fabianhartmann2/LandyHeater-Board/hardware/01_Power_Input_USB.kicad_sch

## KiCad design hardware/01_Power_Input_USB.kicad_sch (2026-09-07, an earlier design)

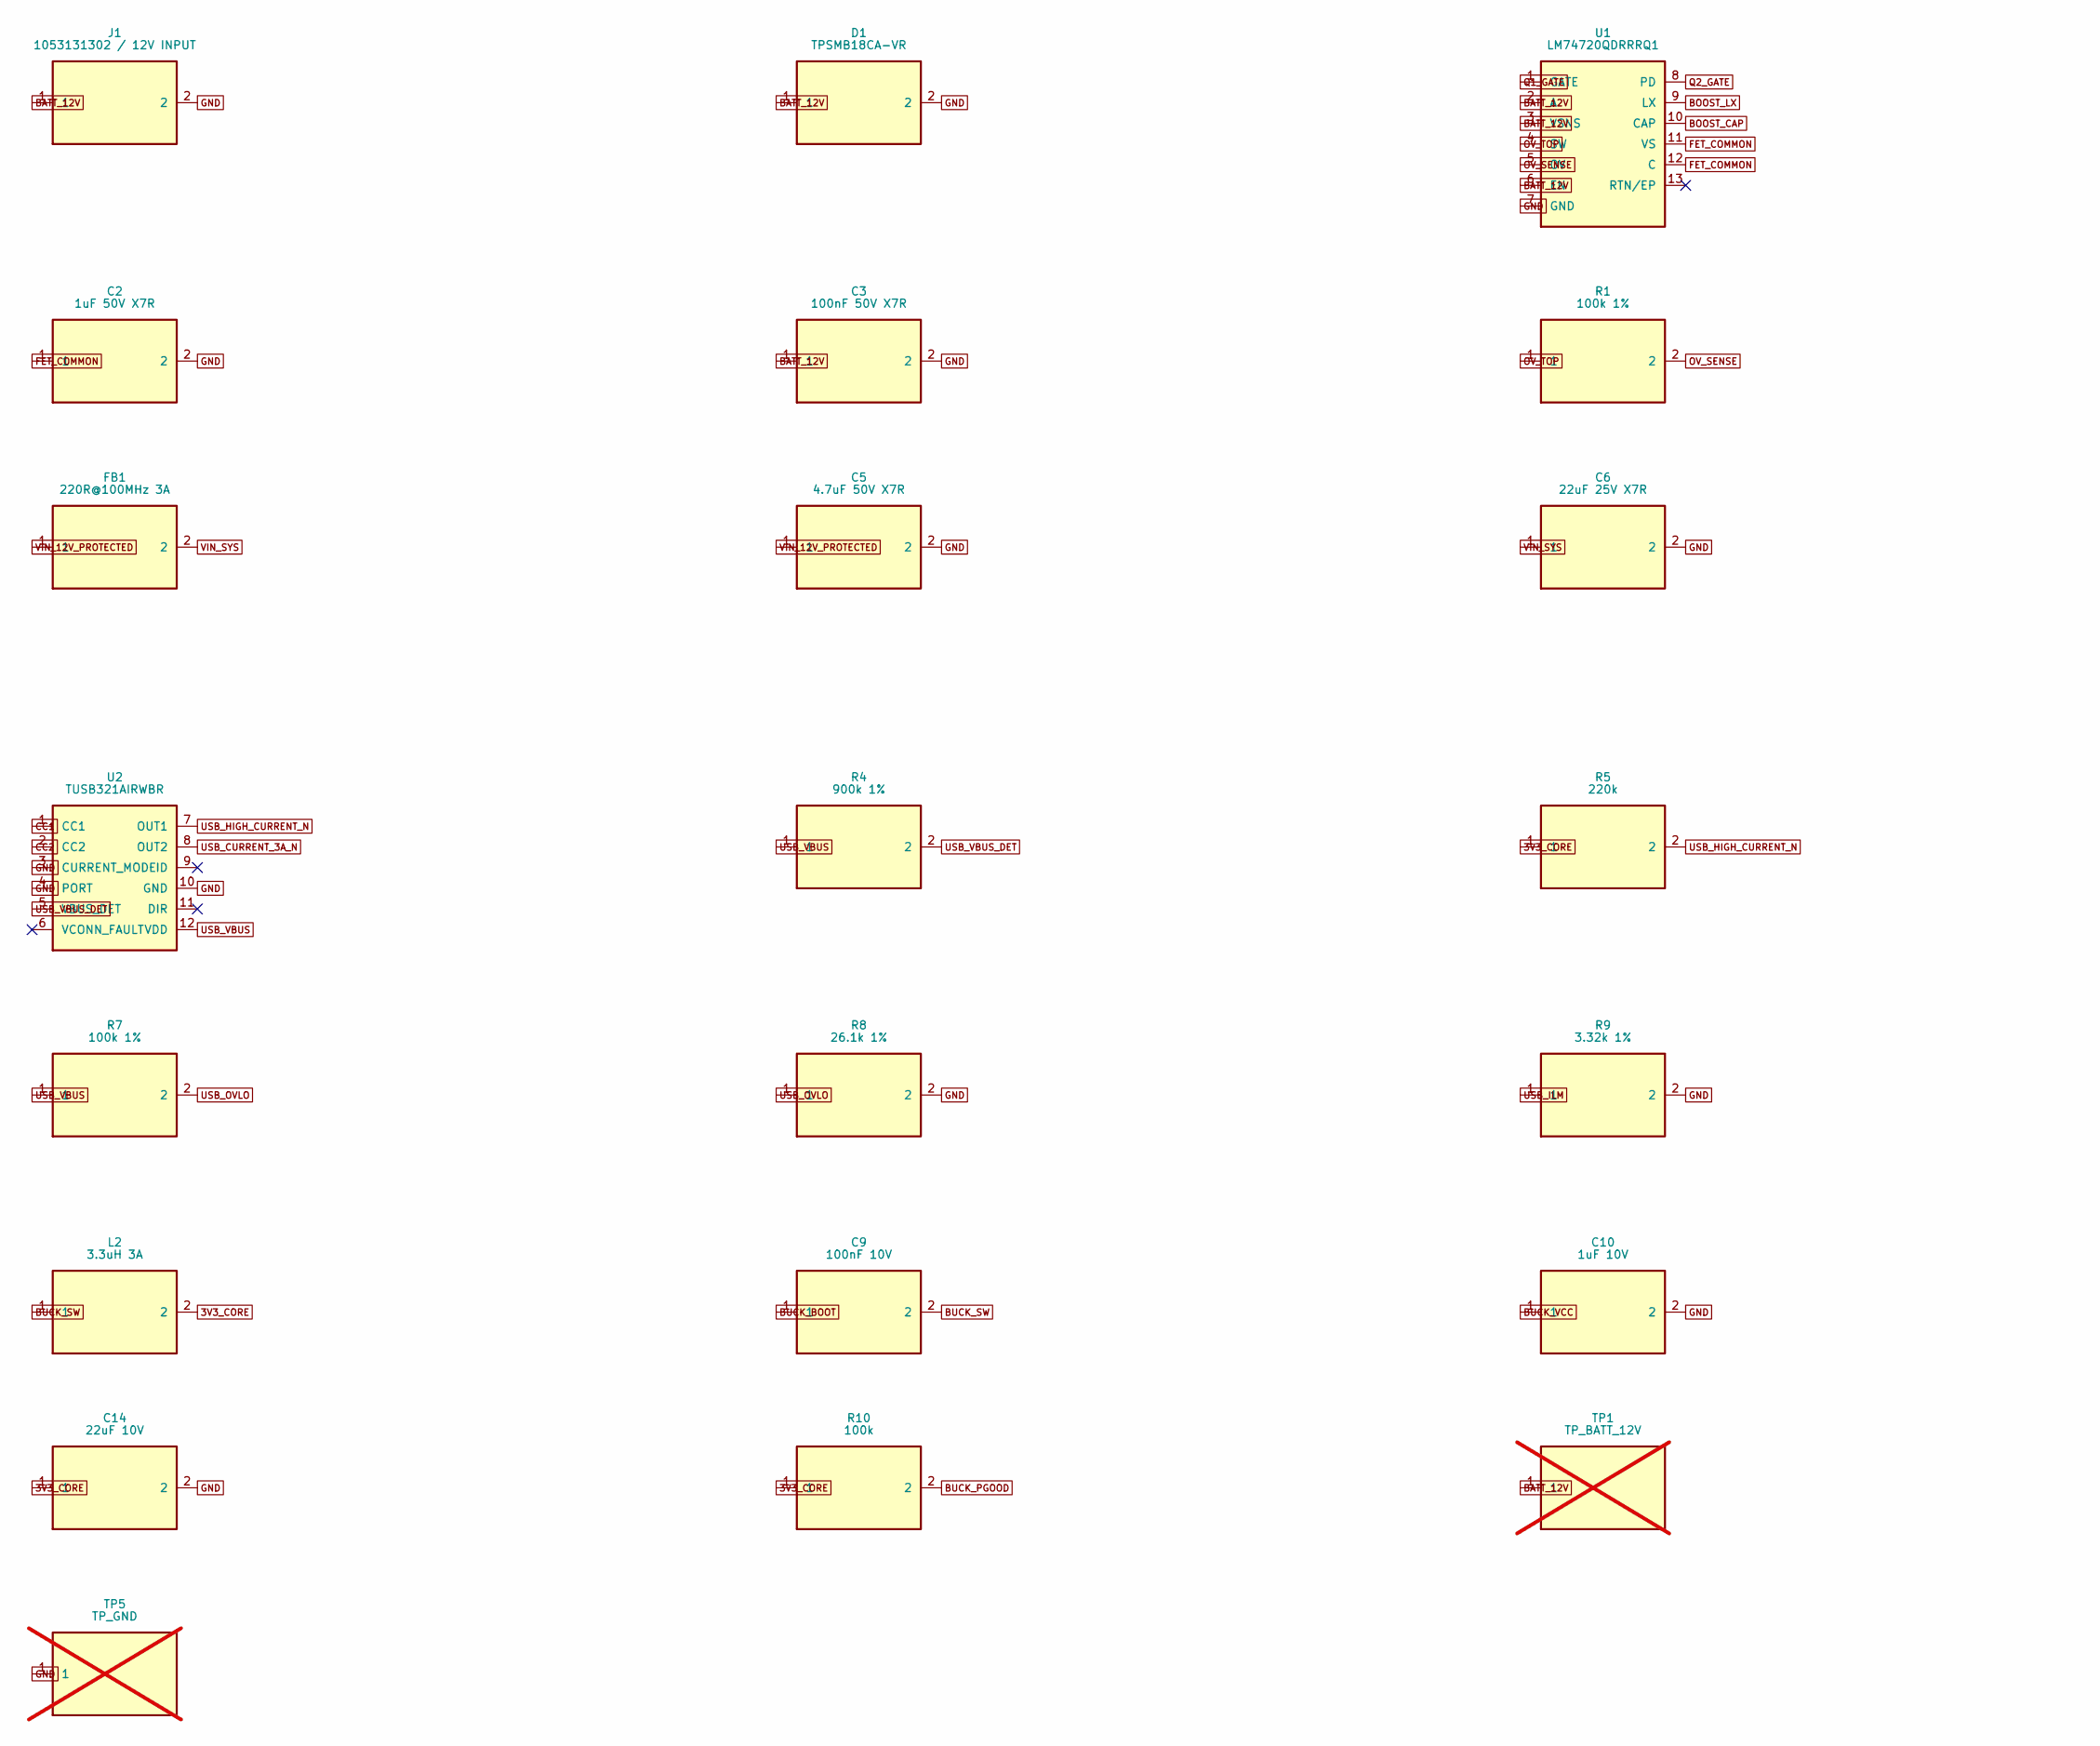
[picture p8: schematic 01_Power_Input_USB.kicad_sch, part in row 1, column 1]

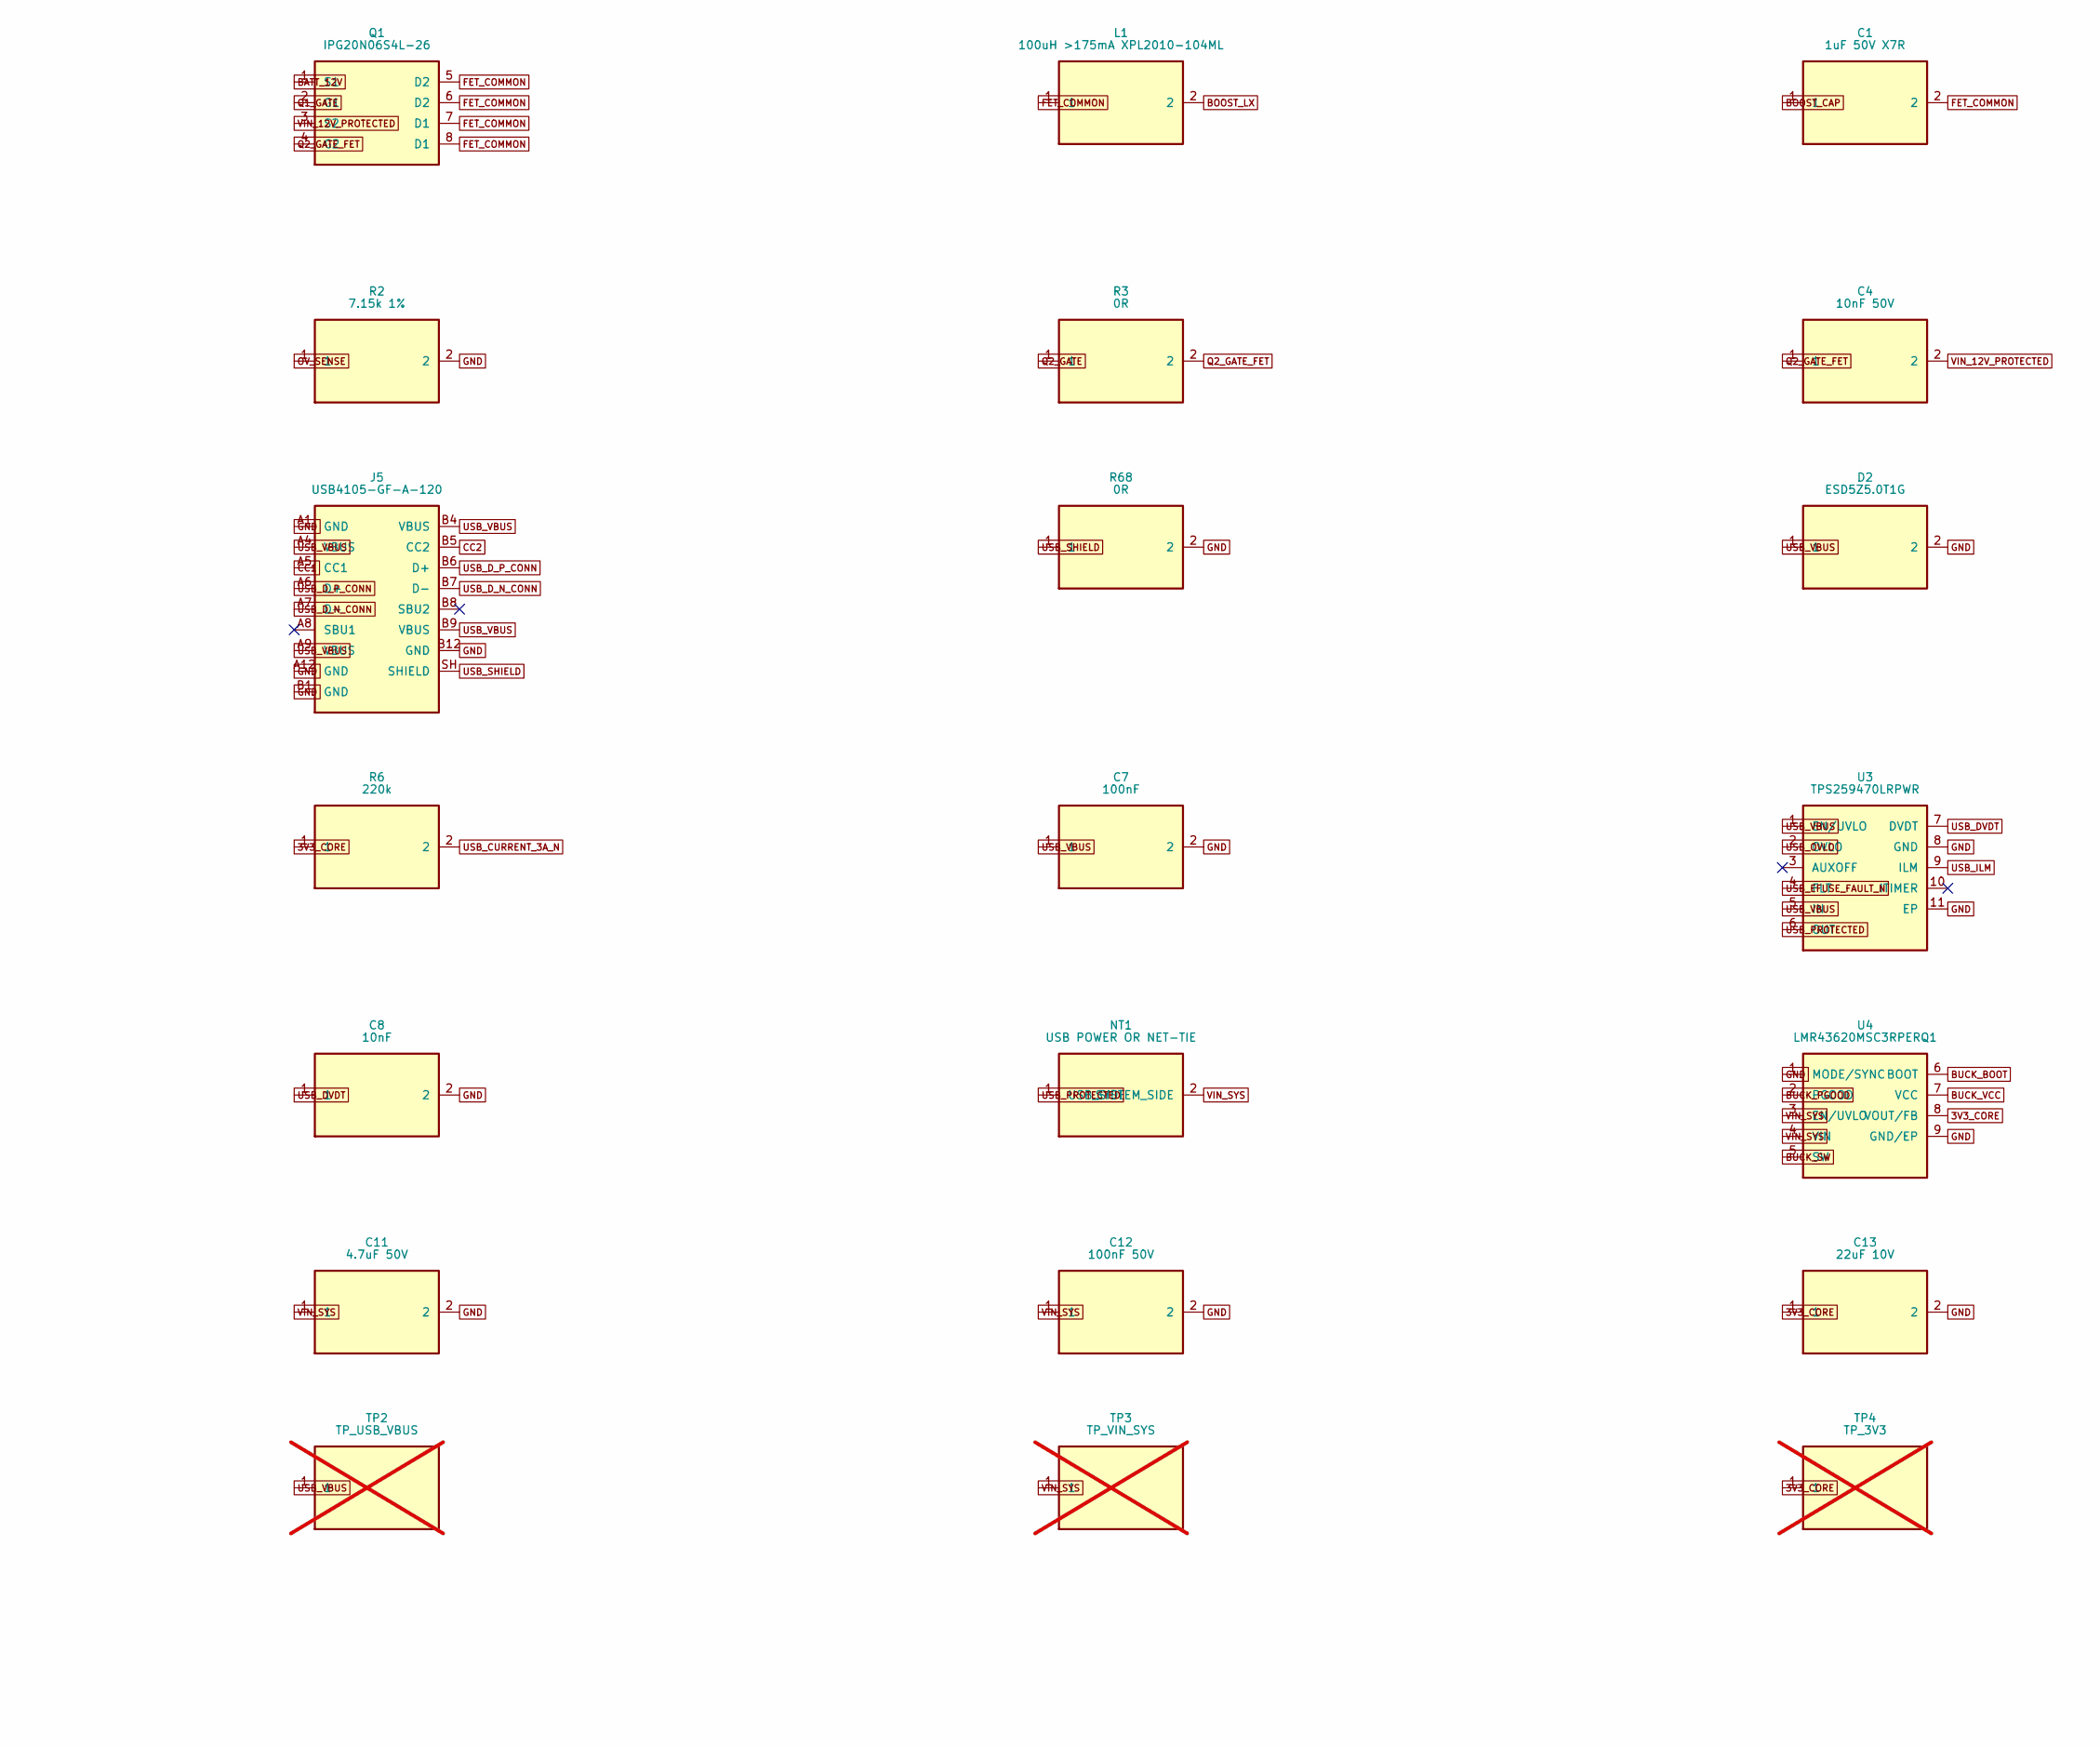
[picture p9: schematic 01_Power_Input_USB.kicad_sch, part in row 1, column 2]

Parts:
C1, C2: 1uF 50V X7R; C_0805_2012Metric_Pad1.18x1.45mm_HandSolder
C3: 100nF 50V X7R; C_0603_1608Metric_Pad1.08x0.95mm_HandSolder
C4: 10nF 50V; C_0603_1608Metric_Pad1.08x0.95mm_HandSolder
C5: 4.7uF 50V X7R; C_0805_2012Metric_Pad1.18x1.45mm_HandSolder
C6: 22uF 25V X7R; C_1210_3225Metric_Pad1.33x2.70mm_HandSolder
C7: 100nF; C_0603_1608Metric_Pad1.08x0.95mm_HandSolder
C8: 10nF; C_0603_1608Metric_Pad1.08x0.95mm_HandSolder
C9: 100nF 10V; C_0603_1608Metric_Pad1.08x0.95mm_HandSolder
C10: 1uF 10V; C_0603_1608Metric_Pad1.08x0.95mm_HandSolder
C11: 4.7uF 50V; C_0805_2012Metric_Pad1.18x1.45mm_HandSolder
C12: 100nF 50V; C_0603_1608Metric_Pad1.08x0.95mm_HandSolder
C13, C14: 22uF 10V; C_0805_2012Metric_Pad1.18x1.45mm_HandSolder
D1: TPSMB18CA-VR; D_SMB; MPN TPSMB18CA-VR
D2: ESD5Z5.0T1G; D_SOD-523; MPN ESD5Z5.0T1G
FB1: 220R@100MHz 3A; L_0805_2012Metric_Pad1.05x1.20mm_HandSolder; MPN MPZ2012S221A
J1: 1053131302 / 12V INPUT; Molex_Nano-Fit_105313-xx02_1x02_P2.50mm_Horizontal; MPN 1053131302
J5: USB4105-GF-A-120; USB_C_Receptacle_GCT_USB4105-xx-A_16P_TopMnt_Horizontal; MPN USB4105-GF-A-120
L1: 100uH >175mA XPL2010-104ML; L_0805_2012Metric_Pad1.05x1.20mm_HandSolder; MPN XPL2010-104ML
L2: 3.3uH 3A; L_Coilcraft_XAL4020-XXX; MPN XAL4020-332MEB
NT1: USB POWER OR NET-TIE; NetTie-2_SMD_Pad0.5mm
Q1: IPG20N06S4L-26; PROVISIONAL_Infineon_PG-TDSON-8-4_Dual; MPN IPG20N06S4L-26
R1, R7: 100k 1%; R_0603_1608Metric_Pad0.98x0.95mm_HandSolder
R2: 7.15k 1%; R_0603_1608Metric_Pad0.98x0.95mm_HandSolder
R3, R68: 0R; R_0603_1608Metric_Pad0.98x0.95mm_HandSolder
R4: 900k 1%; R_0603_1608Metric_Pad0.98x0.95mm_HandSolder
R5, R6: 220k; R_0603_1608Metric_Pad0.98x0.95mm_HandSolder
R8: 26.1k 1%; R_0603_1608Metric_Pad0.98x0.95mm_HandSolder
R9: 3.32k 1%; R_0603_1608Metric_Pad0.98x0.95mm_HandSolder
R10: 100k; R_0603_1608Metric_Pad0.98x0.95mm_HandSolder
TP1: TP_BATT_12V; TestPoint_Pad_D1.5mm; not fitted
TP2: TP_USB_VBUS; TestPoint_Pad_D1.5mm; not fitted
TP3: TP_VIN_SYS; TestPoint_Pad_D1.5mm; not fitted
TP4: TP_3V3; TestPoint_Pad_D1.5mm; not fitted
TP5: TP_GND; TestPoint_Pad_D1.5mm; not fitted
U1: LM74720QDRRRQ1; WSON-12-1EP_3x3mm_P0.5mm_EP1.5x2.5mm_ThermalVias; MPN LM74720QDRRRQ1
U2: TUSB321AIRWBR; Texas_X2QFN-12_1.6x1.6mm_P0.4mm; MPN TUSB321AIRWBR
U3: TPS259470LRPWR; LQFN-10-1EP_2x2mm_P0.5mm_EP0.7x0.7mm; MPN TPS259470LRPWR
U4: LMR43620MSC3RPERQ1; Texas_RPE0009A_VQFN-HR-9_2x2mm; MPN LMR43620MSC3RPERQ1

Connections:
3V3_CORE: C13.1, C14.1, L2.2, R5.1, R6.1, R10.1, TP4.1, U4.8 (VOUT/FB)
BATT_12V: C3.1, D1.1, J1.1, Q1.1 (S1), TP1.1, U1.2 (A), U1.3 (VSNS), U1.6 (EN)
BOOST_CAP: C1.1, U1.10 (CAP)
BOOST_LX: L1.2, U1.9 (LX)
BUCK_BOOT: C9.1, U4.6 (BOOT)
BUCK_PGOOD: R10.2, U4.2 (PGOOD)
BUCK_SW: C9.2, L2.1, U4.5 (SW)
BUCK_VCC: C10.1, U4.7 (VCC)
CC1: J5.A5 (CC1), U2.1 (CC1)
CC2: J5.B5 (CC2), U2.2 (CC2)
FET_COMMON: C1.2, C2.1, L1.1, Q1.5 (D2), Q1.6 (D2), Q1.7 (D1), Q1.8 (D1), U1.11 (VS), U1.12 (C)
GND: C2.2, C3.2, C5.2, C6.2, C7.2, C8.2, C10.2, C11.2, C12.2, C13.2, C14.2, D1.2, D2.2, J1.2, J5.A1 (GND), J5.A12 (GND), J5.B1 (GND), J5.B12 (GND), R2.2, R8.2, R9.2, R68.2, TP5.1, U1.7 (GND), U2.3 (CURRENT_MODE), U2.4 (PORT), U2.10 (GND), U3.8 (GND), U3.11 (EP), U4.1 (MODE/SYNC), U4.9 (GND/EP)
OV_SENSE: R1.2, R2.1, U1.5 (OV)
OV_TOP: R1.1, U1.4 (SW)
Q1_GATE: Q1.2 (G1), U1.1 (GATE)
Q2_GATE: R3.1, U1.8 (PD)
Q2_GATE_FET: C4.1, Q1.4 (G2), R3.2
USB_CURRENT_3A_N: R6.2, U2.8 (OUT2)
USB_DVDT: C8.1, U3.7 (DVDT)
USB_D_N_CONN: J5.A7 (D-), J5.B7 (D-)
USB_D_P_CONN: J5.A6 (D+), J5.B6 (D+)
USB_EFUSE_FAULT_N: U3.4 (FLT)
USB_HIGH_CURRENT_N: R5.2, U2.7 (OUT1)
USB_ILM: R9.1, U3.9 (ILM)
USB_OVLO: R7.2, R8.1, U3.2 (OVLO)
USB_PROTECTED: NT1.1 (USB_SIDE), U3.6 (OUT)
USB_SHIELD: J5.SH (SHIELD), R68.1
USB_VBUS: C7.1, D2.1, J5.A4 (VBUS), J5.A9 (VBUS), J5.B4 (VBUS), J5.B9 (VBUS), R4.1, R7.1, TP2.1, U2.12 (VDD), U3.1 (EN/UVLO), U3.5 (IN)
USB_VBUS_DET: R4.2, U2.5 (VBUS_DET)
VIN_12V_PROTECTED: C4.2, C5.1, FB1.1, Q1.3 (S2)
VIN_SYS: C6.1, C11.1, C12.1, FB1.2, NT1.2 (SYSTEM_SIDE), TP3.1, U4.3 (EN/UVLO), U4.4 (VIN)
