fabianhartmann2/LandyHeater-Board/hardware/02_ESP32_USB_Reset.kicad_sch

## KiCad design hardware/02_ESP32_USB_Reset.kicad_sch (2026-09-07, an earlier design)

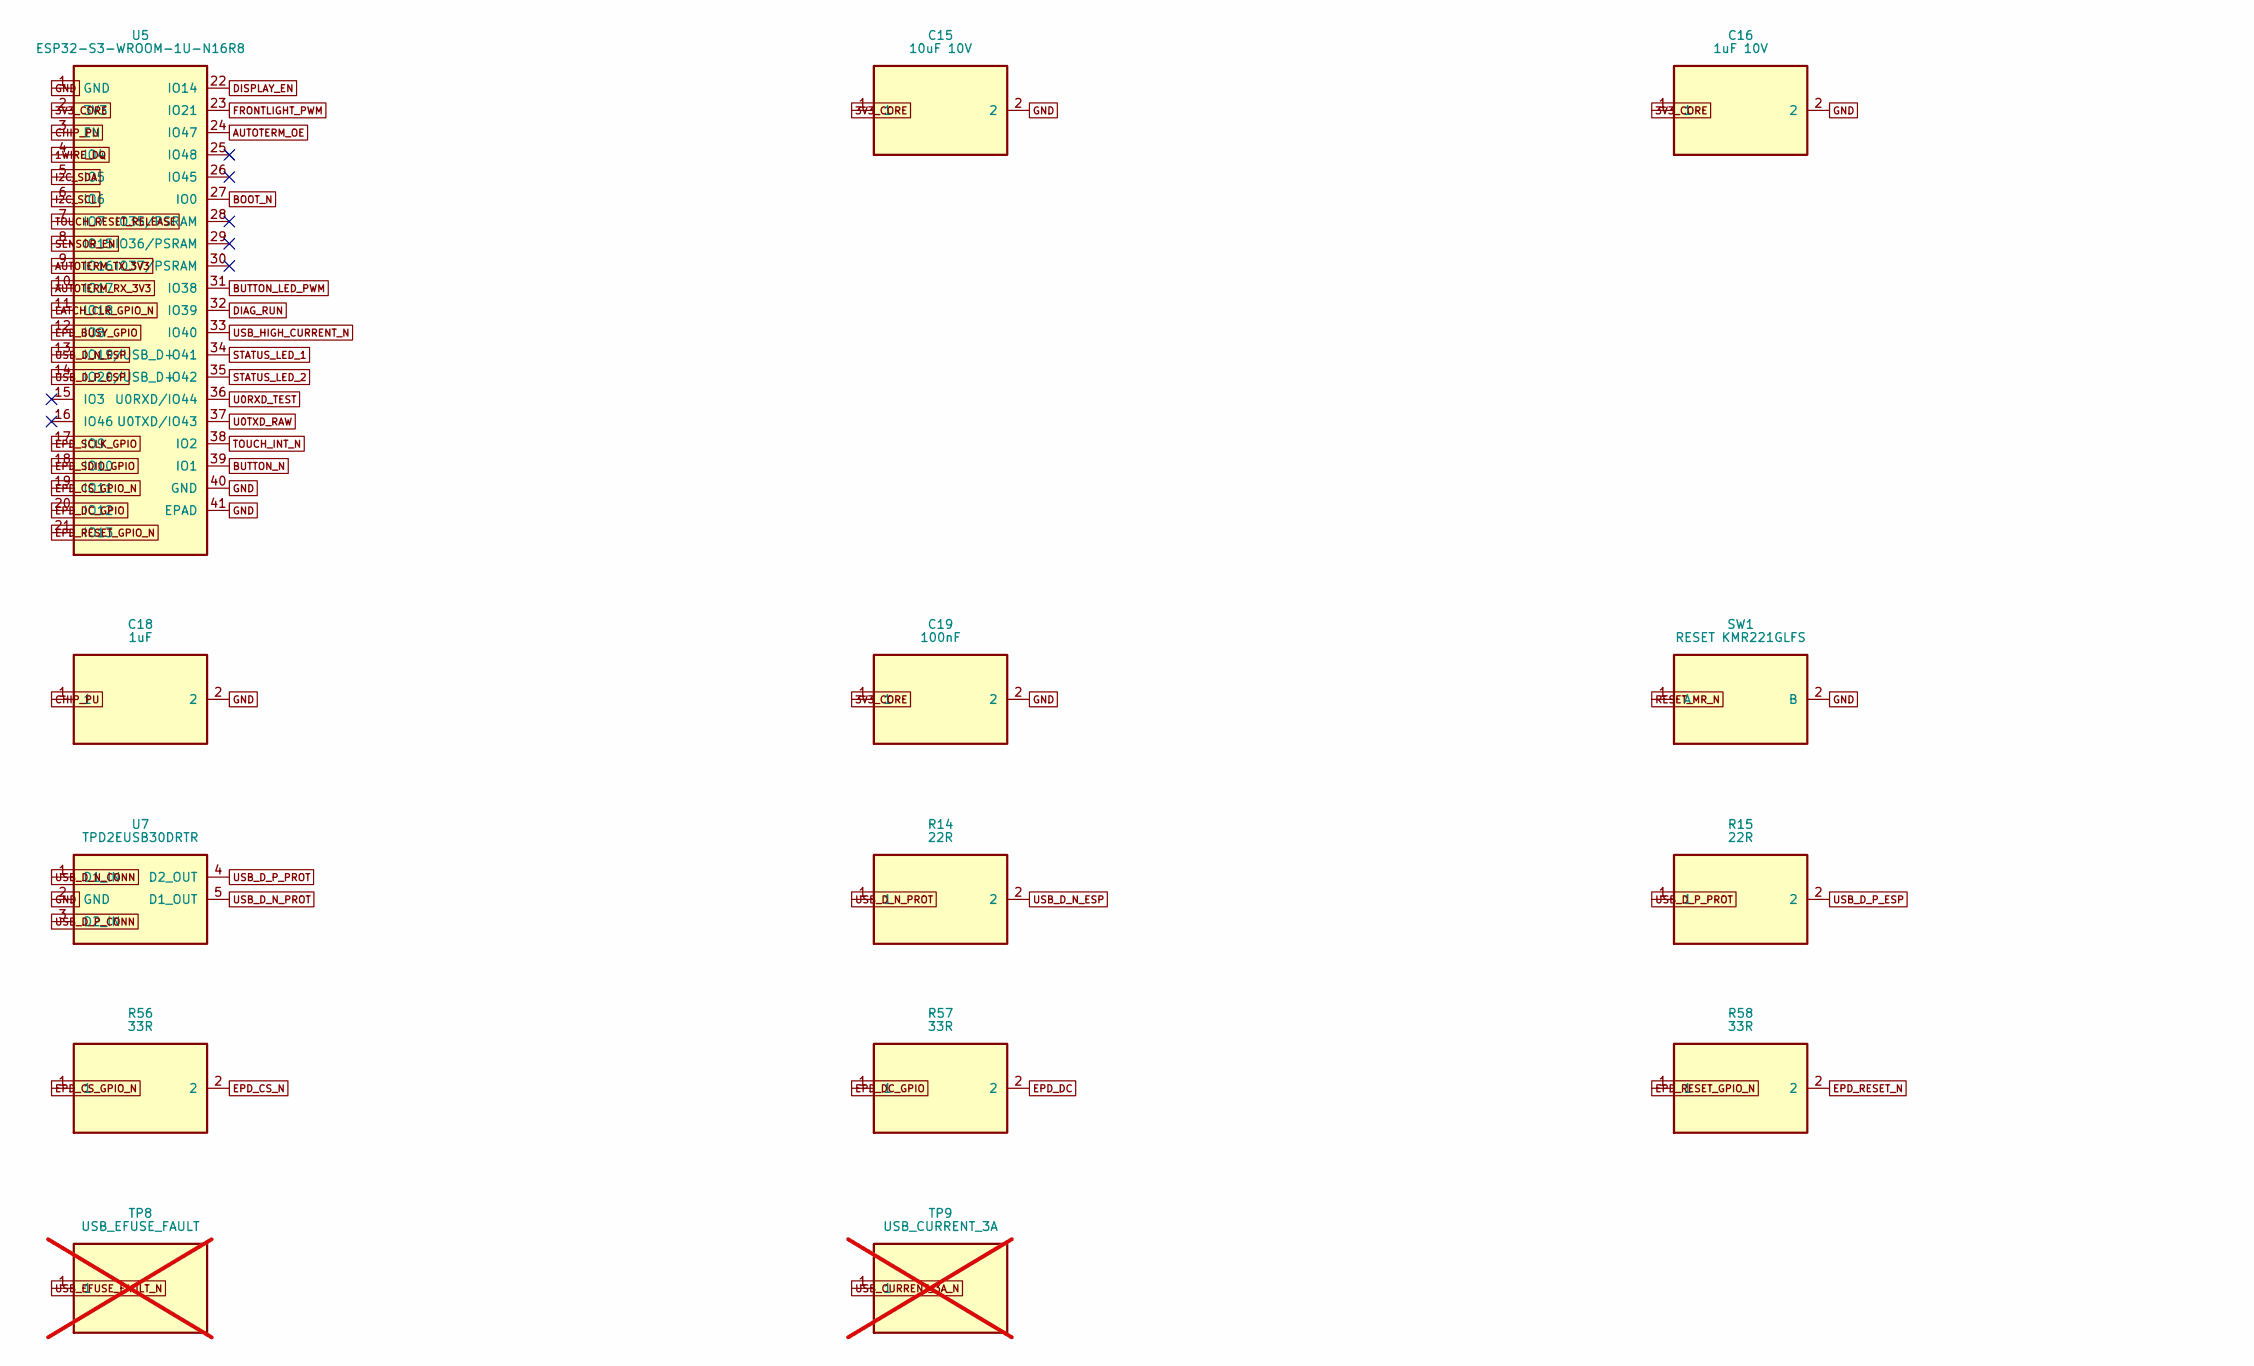
[picture p10: schematic 02_ESP32_USB_Reset.kicad_sch, part in row 1, column 1]

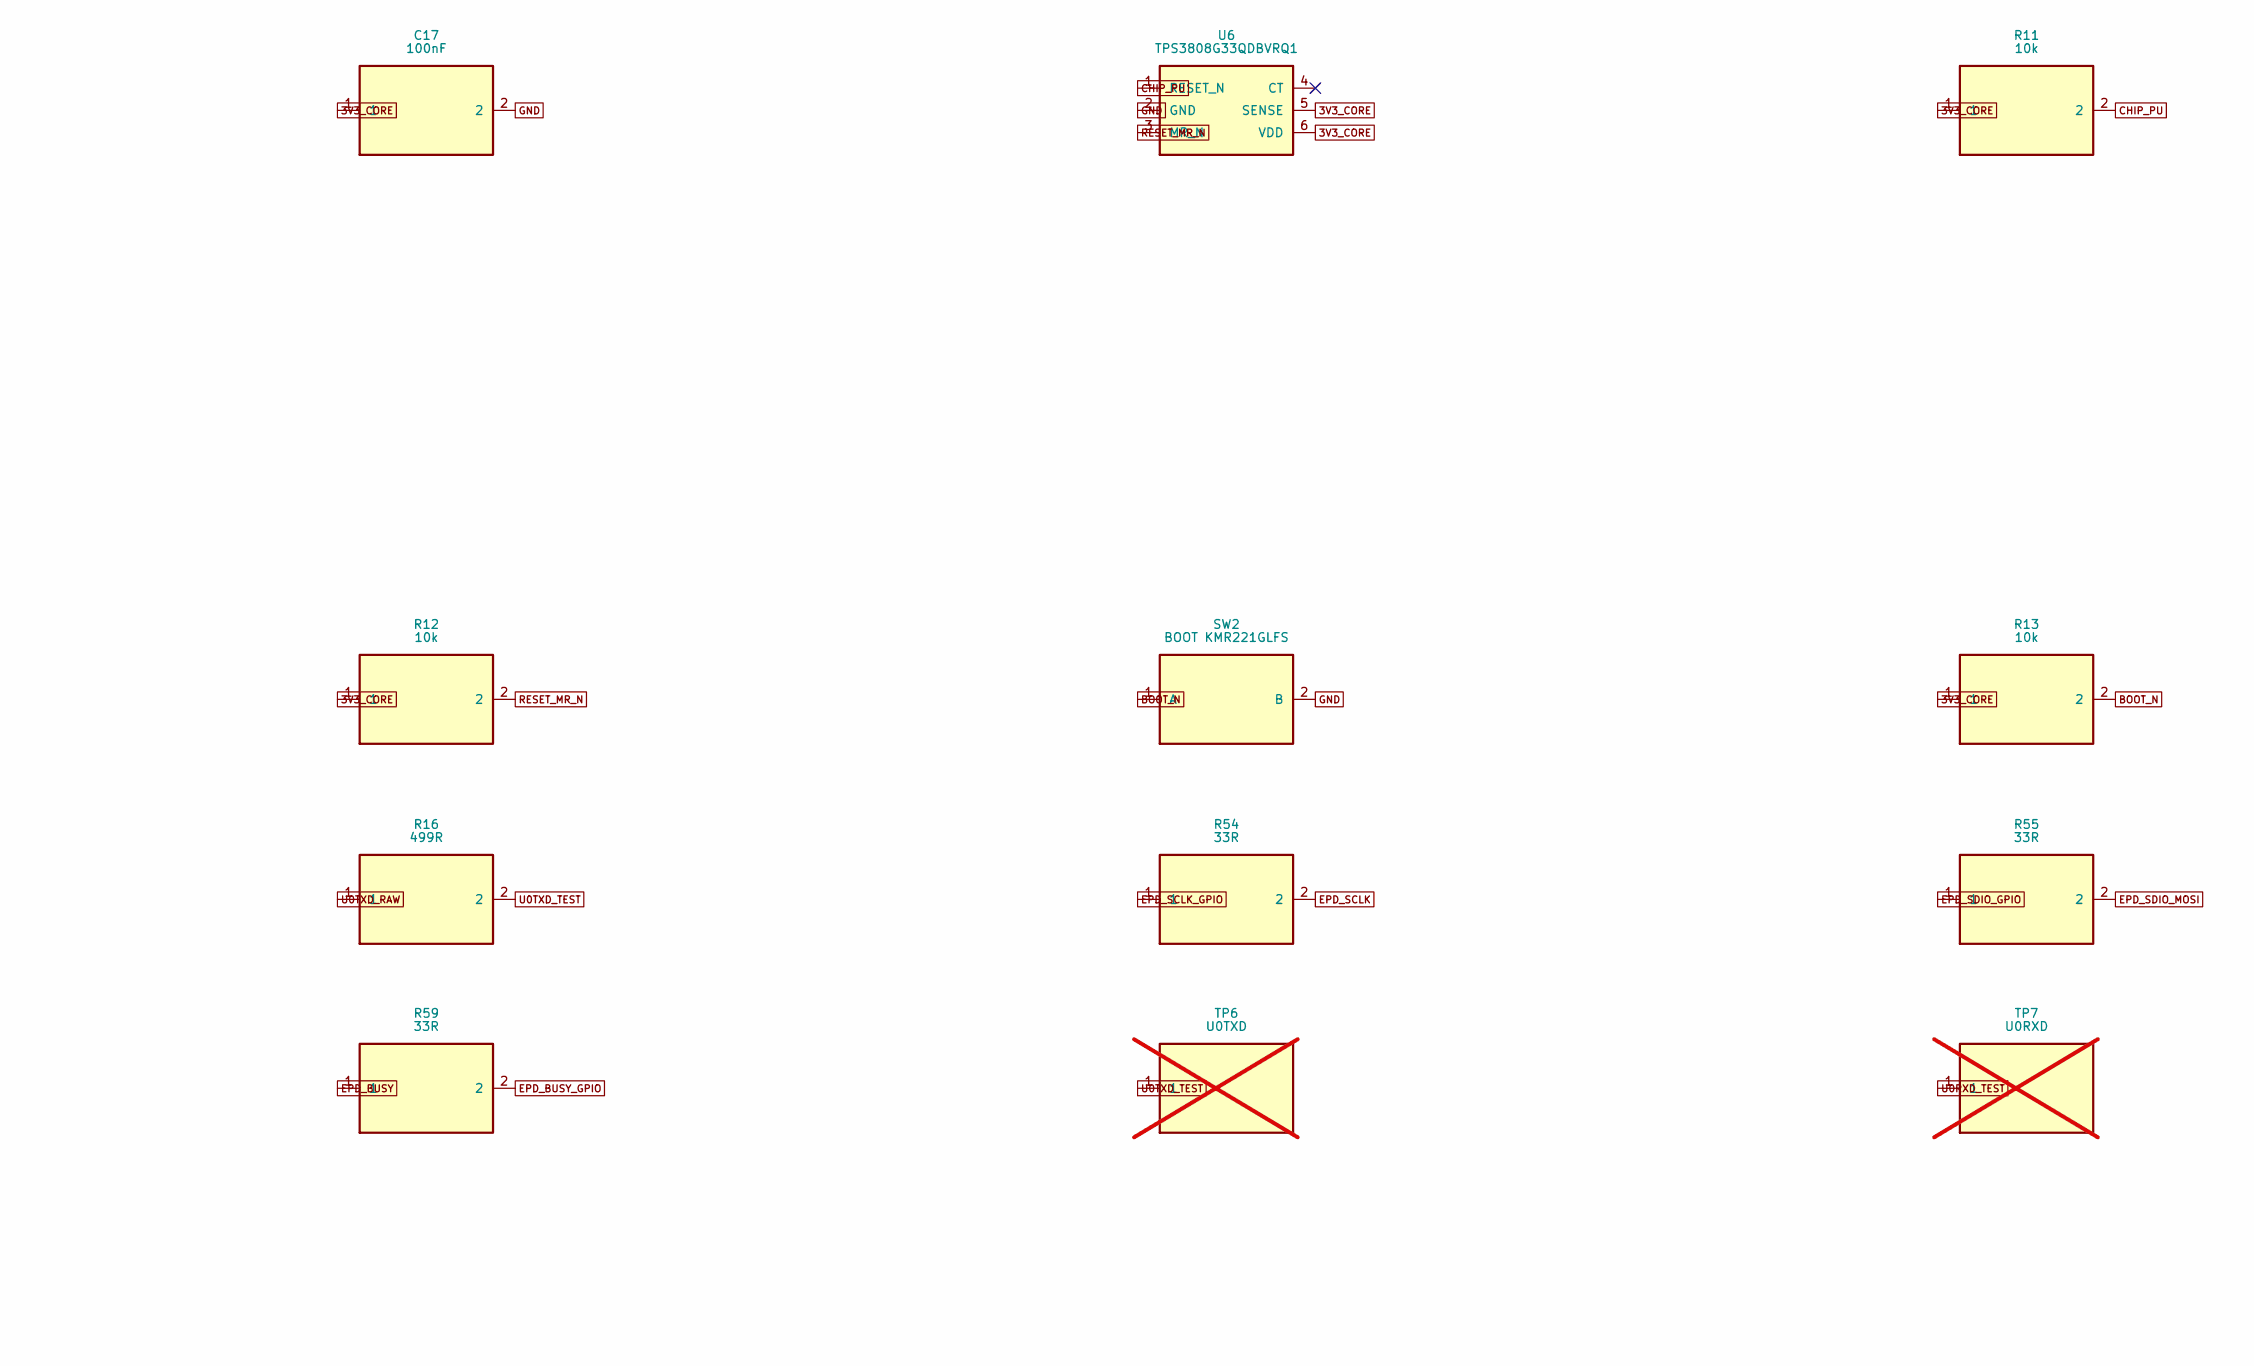
[picture p11: schematic 02_ESP32_USB_Reset.kicad_sch, part in row 1, column 2]

Parts:
C15: 10uF 10V; C_0805_2012Metric_Pad1.18x1.45mm_HandSolder
C16: 1uF 10V; C_0603_1608Metric_Pad1.08x0.95mm_HandSolder
C17, C19: 100nF; C_0603_1608Metric_Pad1.08x0.95mm_HandSolder
C18: 1uF; C_0603_1608Metric_Pad1.08x0.95mm_HandSolder
R11, R12, R13: 10k; R_0603_1608Metric_Pad0.98x0.95mm_HandSolder
R14, R15: 22R; R_0603_1608Metric_Pad0.98x0.95mm_HandSolder
R16: 499R; R_0603_1608Metric_Pad0.98x0.95mm_HandSolder
R54, R55, R56, R57, R58, R59: 33R; R_0603_1608Metric_Pad0.98x0.95mm_HandSolder
SW1: RESET KMR221GLFS; SW_Push_1P1T_NO_CK_KMR2; MPN KMR221GLFS
SW2: BOOT KMR221GLFS; SW_Push_1P1T_NO_CK_KMR2; MPN KMR221GLFS
TP6: U0TXD; TestPoint_Pad_D1.0mm; not fitted
TP7: U0RXD; TestPoint_Pad_D1.0mm; not fitted
TP8: USB_EFUSE_FAULT; TestPoint_Pad_D1.0mm; not fitted
TP9: USB_CURRENT_3A; TestPoint_Pad_D1.0mm; not fitted
U5: ESP32-S3-WROOM-1U-N16R8; ESP32-S3-WROOM-1U; MPN ESP32-S3-WROOM-1U-N16R8
U6: TPS3808G33QDBVRQ1; SOT-23-6; MPN TPS3808G33QDBVRQ1
U7: TPD2EUSB30DRTR; SOT-23-5; MPN TPD2EUSB30DRTR

Connections:
1WIRE_DQ: U5.4 (IO4)
3V3_CORE: C15.1, C16.1, C17.1, C19.1, R11.1, R12.1, R13.1, U5.2 (3V3), U6.5 (SENSE), U6.6 (VDD)
AUTOTERM_OE: U5.24 (IO47)
AUTOTERM_RX_3V3: U5.10 (IO17)
AUTOTERM_TX_3V3: U5.9 (IO16)
BOOT_N: R13.2, SW2.1 (A), U5.27 (IO0)
BUTTON_LED_PWM: U5.31 (IO38)
BUTTON_N: U5.39 (IO1)
CHIP_PU: C18.1, R11.2, U5.3 (EN), U6.1 (RESET_N)
DIAG_RUN: U5.32 (IO39)
DISPLAY_EN: U5.22 (IO14)
EPD_BUSY: R59.1
EPD_BUSY_GPIO: R59.2, U5.12 (IO8)
EPD_CS_GPIO_N: R56.1, U5.19 (IO11)
EPD_CS_N: R56.2
EPD_DC: R57.2
EPD_DC_GPIO: R57.1, U5.20 (IO12)
EPD_RESET_GPIO_N: R58.1, U5.21 (IO13)
EPD_RESET_N: R58.2
EPD_SCLK: R54.2
EPD_SCLK_GPIO: R54.1, U5.17 (IO9)
EPD_SDIO_GPIO: R55.1, U5.18 (IO10)
EPD_SDIO_MOSI: R55.2
FRONTLIGHT_PWM: U5.23 (IO21)
GND: C15.2, C16.2, C17.2, C18.2, C19.2, SW1.2 (B), SW2.2 (B), U5.1 (GND), U5.40 (GND), U5.41 (EPAD), U6.2 (GND), U7.2 (GND)
I2C_SCL: U5.6 (IO6)
I2C_SDA: U5.5 (IO5)
LATCH_CLR_GPIO_N: U5.11 (IO18)
RESET_MR_N: R12.2, SW1.1 (A), U6.3 (MR_N)
SENSOR_EN: U5.8 (IO15)
STATUS_LED_1: U5.34 (IO41)
STATUS_LED_2: U5.35 (IO42)
TOUCH_INT_N: U5.38 (IO2)
TOUCH_RESET_RELEASE: U5.7 (IO7)
U0RXD_TEST: TP7.1, U5.36 (U0RXD/IO44)
U0TXD_RAW: R16.1, U5.37 (U0TXD/IO43)
U0TXD_TEST: R16.2, TP6.1
USB_CURRENT_3A_N: TP9.1
USB_D_N_CONN: U7.1 (D1_IN)
USB_D_N_ESP: R14.2, U5.13 (IO19/USB_D-)
USB_D_N_PROT: R14.1, U7.5 (D1_OUT)
USB_D_P_CONN: U7.3 (D2_IN)
USB_D_P_ESP: R15.2, U5.14 (IO20/USB_D+)
USB_D_P_PROT: R15.1, U7.4 (D2_OUT)
USB_EFUSE_FAULT_N: TP8.1
USB_HIGH_CURRENT_N: U5.33 (IO40)
