fabianhartmann2/LandyHeater-Board/hardware/03_Display_EPaper.kicad_sch

## KiCad design hardware/03_Display_EPaper.kicad_sch (2026-09-07, an earlier design)

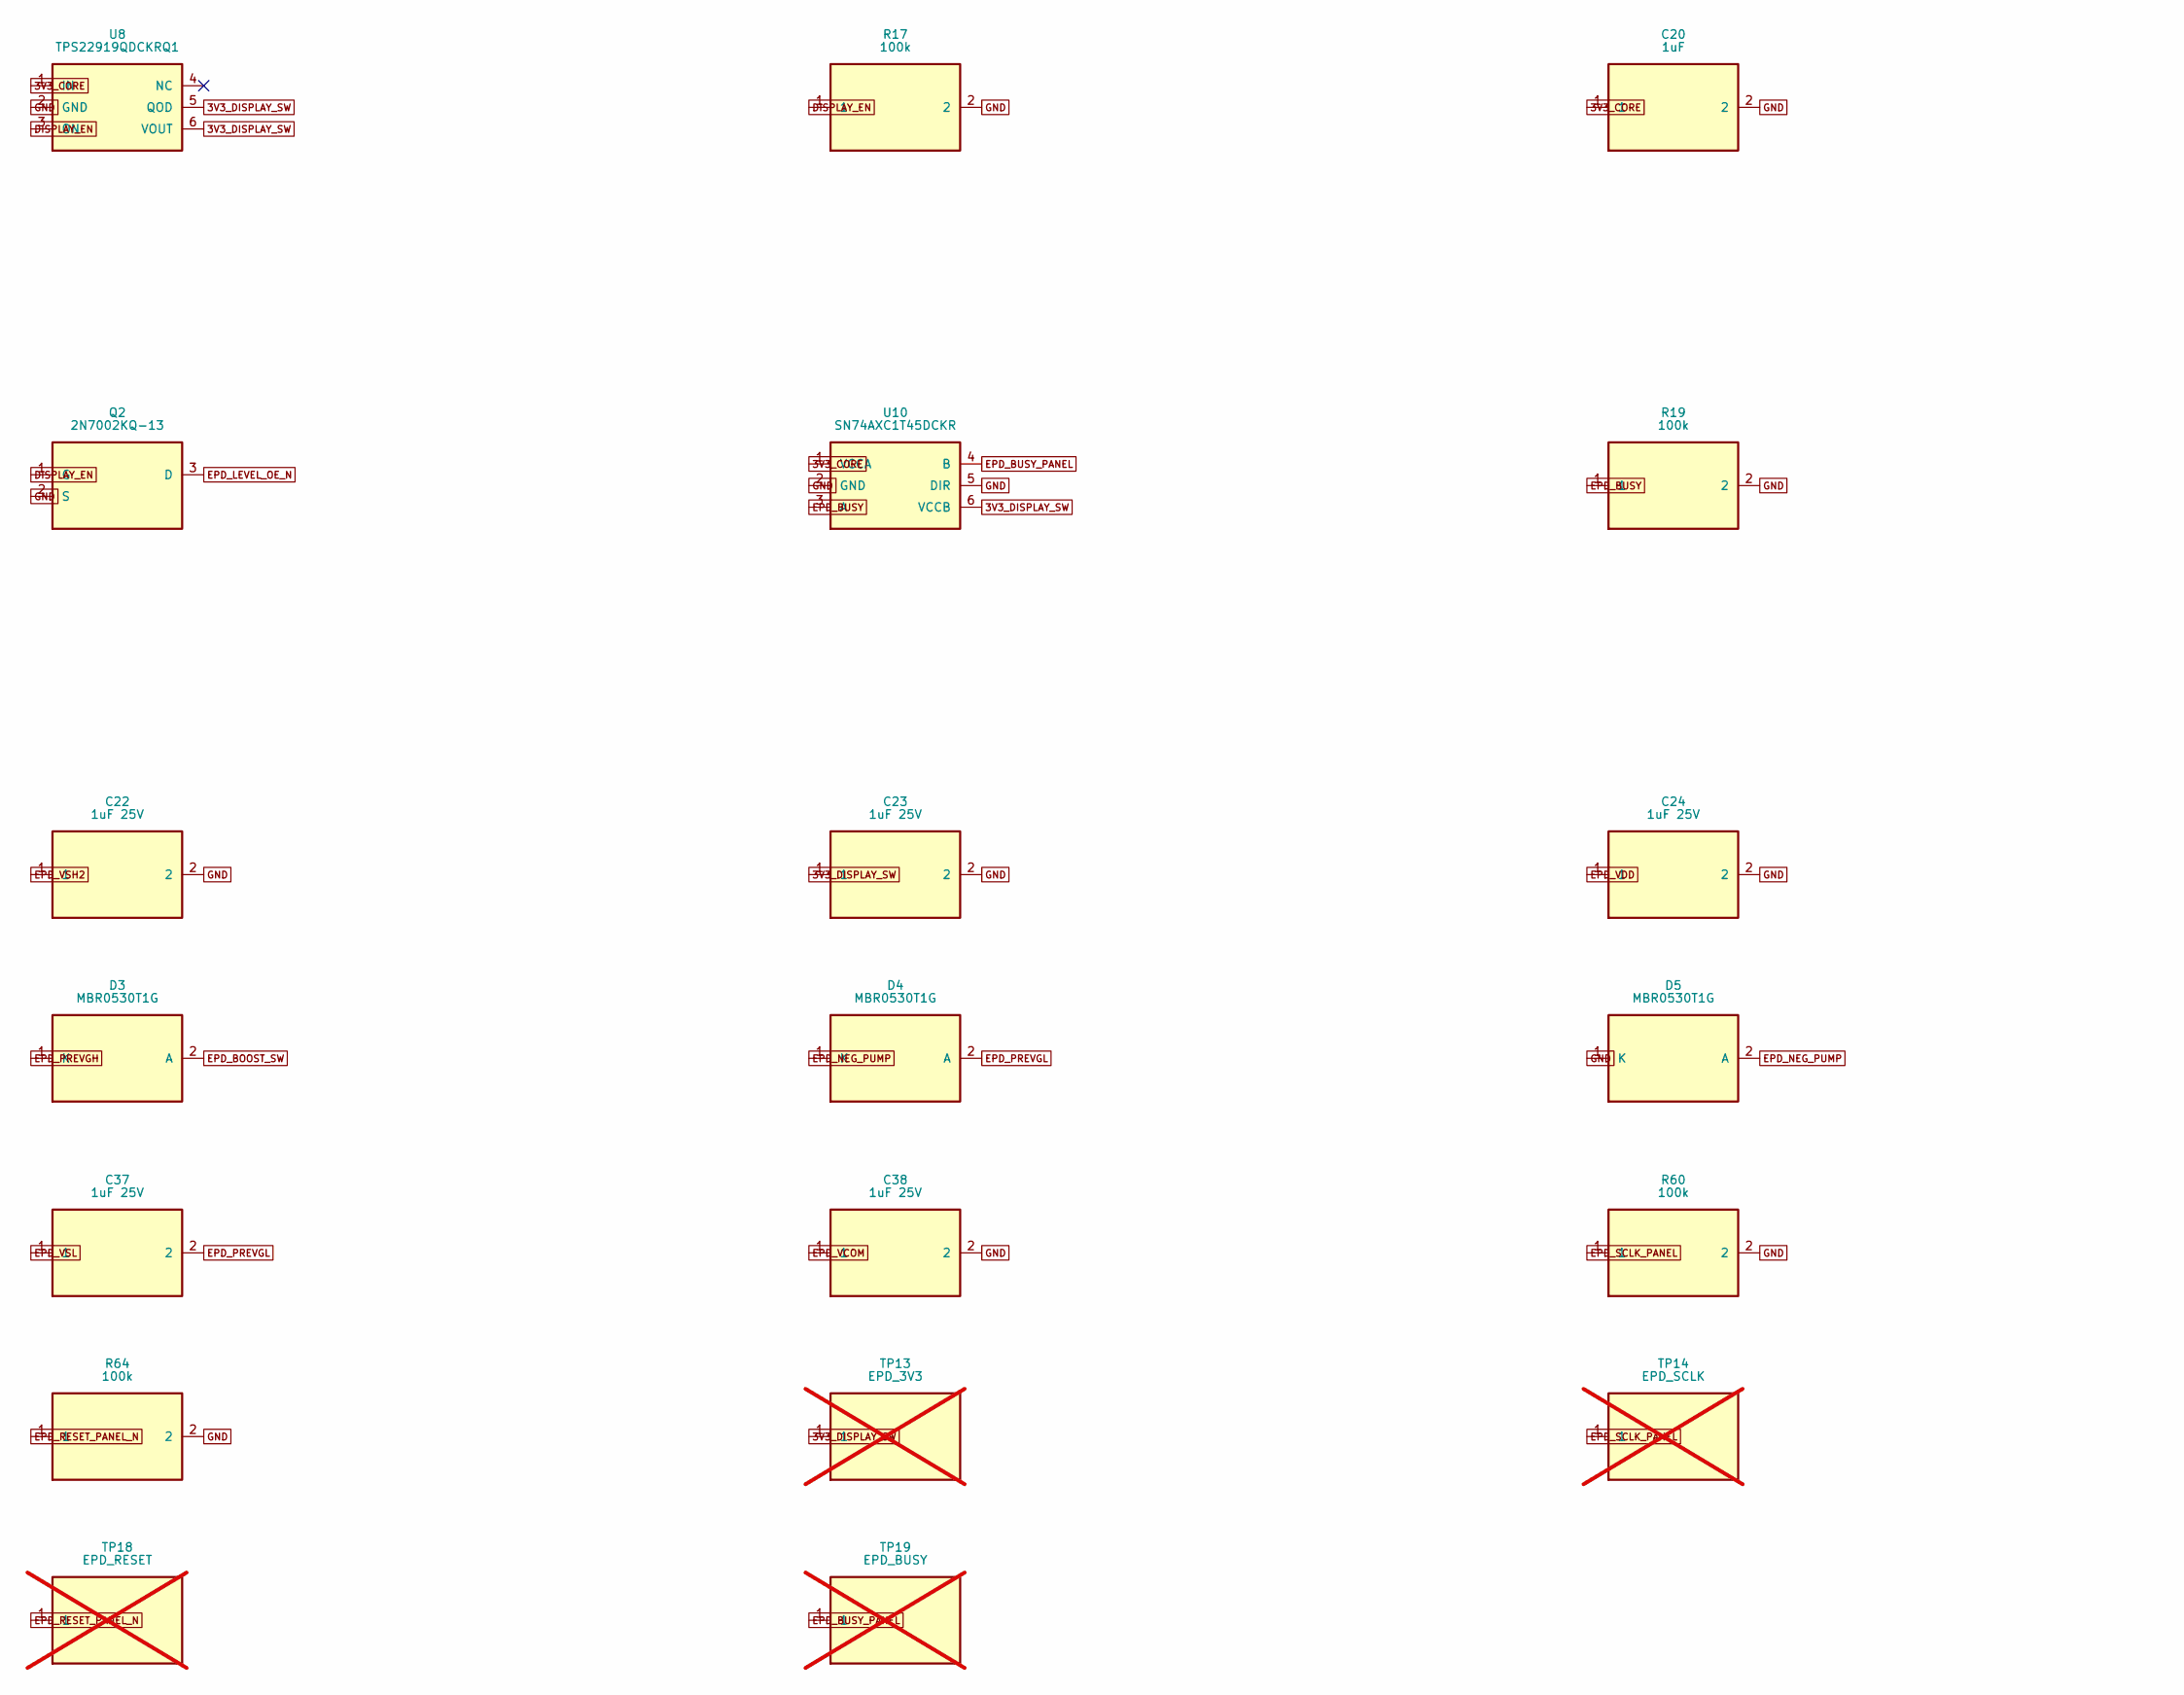
[picture p12: schematic 03_Display_EPaper.kicad_sch, part in row 1, column 1]

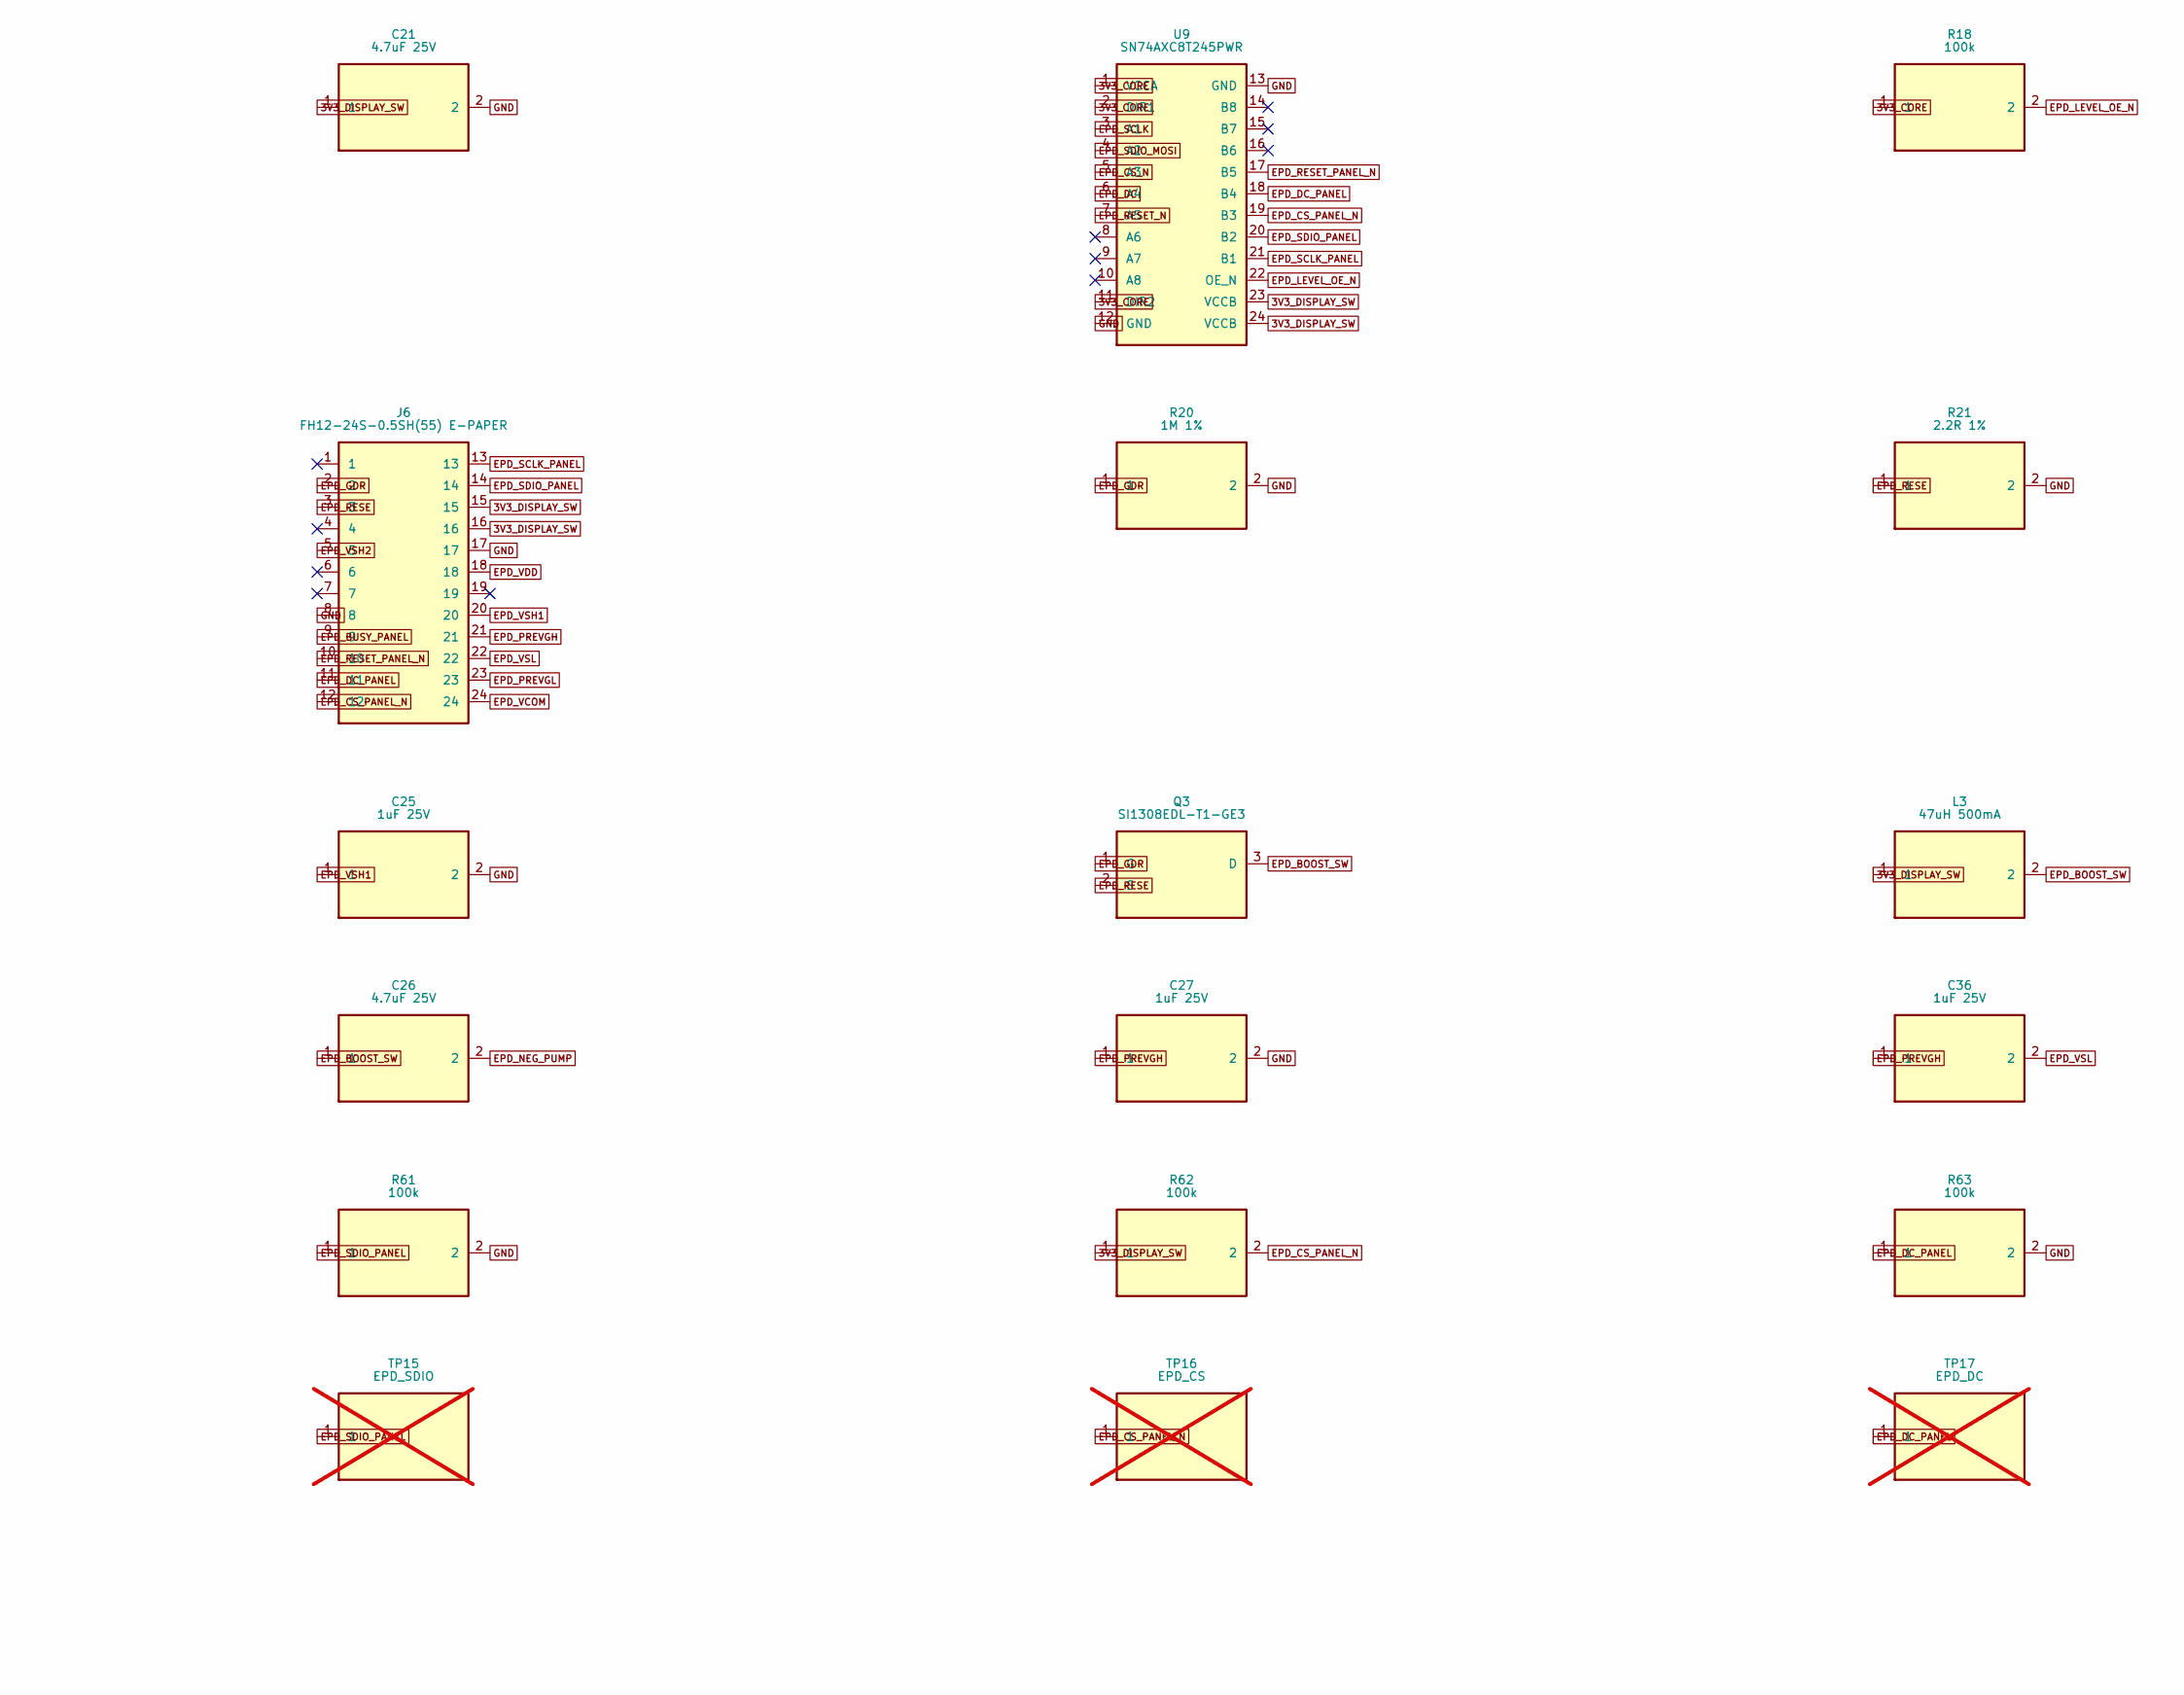
[picture p13: schematic 03_Display_EPaper.kicad_sch, part in row 1, column 2]

Parts:
C20: 1uF; C_0603_1608Metric_Pad1.08x0.95mm_HandSolder
C21, C26: 4.7uF 25V; C_0805_2012Metric_Pad1.18x1.45mm_HandSolder
C22, C23, C24, C25, C27, C36, C37, C38: 1uF 25V; C_0805_2012Metric_Pad1.18x1.45mm_HandSolder
D3, D4, D5: MBR0530T1G; D_SOD-123; MPN MBR0530T1G
J6: FH12-24S-0.5SH(55) E-PAPER; Hirose_FH12-24S-0.5SH_1x24-1MP_P0.50mm_Horizontal; MPN FH12-24S-0.5SH(55)
L3: 47uH 500mA; L_Changjiang_FNR3015S
Q2: 2N7002KQ-13; SOT-23; MPN 2N7002KQ-13
Q3: SI1308EDL-T1-GE3; SOT-323_SC-70; MPN SI1308EDL-T1-GE3
R17, R18, R19, R60, R61, R62, R63, R64: 100k; R_0603_1608Metric_Pad0.98x0.95mm_HandSolder
R20: 1M 1%; R_0603_1608Metric_Pad0.98x0.95mm_HandSolder
R21: 2.2R 1%; R_0603_1608Metric_Pad0.98x0.95mm_HandSolder
TP13: EPD_3V3; TestPoint_Pad_D1.0mm; not fitted
TP14: EPD_SCLK; TestPoint_Pad_D1.0mm; not fitted
TP15: EPD_SDIO; TestPoint_Pad_D1.0mm; not fitted
TP16: EPD_CS; TestPoint_Pad_D1.0mm; not fitted
TP17: EPD_DC; TestPoint_Pad_D1.0mm; not fitted
TP18: EPD_RESET; TestPoint_Pad_D1.0mm; not fitted
TP19: EPD_BUSY; TestPoint_Pad_D1.0mm; not fitted
U8: TPS22919QDCKRQ1; SOT-363_SC-70-6; MPN TPS22919QDCKRQ1
U9: SN74AXC8T245PWR; TSSOP-24_4.4x7.8mm_P0.65mm; MPN SN74AXC8T245PWR
U10: SN74AXC1T45DCKR; SOT-363_SC-70-6; MPN SN74AXC1T45DCKR

Connections:
3V3_CORE: C20.1, R18.1, U8.1 (IN), U9.1 (VCCA), U9.2 (DIR1), U9.11 (DIR2), U10.1 (VCCA)
3V3_DISPLAY_SW: C21.1, C23.1, J6.15, J6.16, L3.1, R62.1, TP13.1, U8.5 (QOD), U8.6 (VOUT), U9.23 (VCCB), U9.24 (VCCB), U10.6 (VCCB)
DISPLAY_EN: Q2.1 (G), R17.1, U8.3 (ON)
EPD_BOOST_SW: C26.1, D3.2 (A), L3.2, Q3.3 (D)
EPD_BUSY: R19.1, U10.3 (A)
EPD_BUSY_PANEL: J6.9, TP19.1, U10.4 (B)
EPD_CS_N: U9.5 (A3)
EPD_CS_PANEL_N: J6.12, R62.2, TP16.1, U9.19 (B3)
EPD_DC: U9.6 (A4)
EPD_DC_PANEL: J6.11, R63.1, TP17.1, U9.18 (B4)
EPD_GDR: J6.2, Q3.1 (G), R20.1
EPD_LEVEL_OE_N: Q2.3 (D), R18.2, U9.22 (OE_N)
EPD_NEG_PUMP: C26.2, D4.1 (K), D5.2 (A)
EPD_PREVGH: C27.1, C36.1, D3.1 (K), J6.21
EPD_PREVGL: C37.2, D4.2 (A), J6.23
EPD_RESE: J6.3, Q3.2 (S), R21.1
EPD_RESET_N: U9.7 (A5)
EPD_RESET_PANEL_N: J6.10, R64.1, TP18.1, U9.17 (B5)
EPD_SCLK: U9.3 (A1)
EPD_SCLK_PANEL: J6.13, R60.1, TP14.1, U9.21 (B1)
EPD_SDIO_MOSI: U9.4 (A2)
EPD_SDIO_PANEL: J6.14, R61.1, TP15.1, U9.20 (B2)
EPD_VCOM: C38.1, J6.24
EPD_VDD: C24.1, J6.18
EPD_VSH1: C25.1, J6.20
EPD_VSH2: C22.1, J6.5
EPD_VSL: C36.2, C37.1, J6.22
GND: C20.2, C21.2, C22.2, C23.2, C24.2, C25.2, C27.2, C38.2, D5.1 (K), J6.8, J6.17, Q2.2 (S), R17.2, R19.2, R20.2, R21.2, R60.2, R61.2, R63.2, R64.2, U8.2 (GND), U9.12 (GND), U9.13 (GND), U10.2 (GND), U10.5 (DIR)
