fabianhartmann2/LandyHeater-Board/hardware/04_Touch_RTC.kicad_sch

## KiCad design hardware/04_Touch_RTC.kicad_sch (2026-09-07, an earlier design)

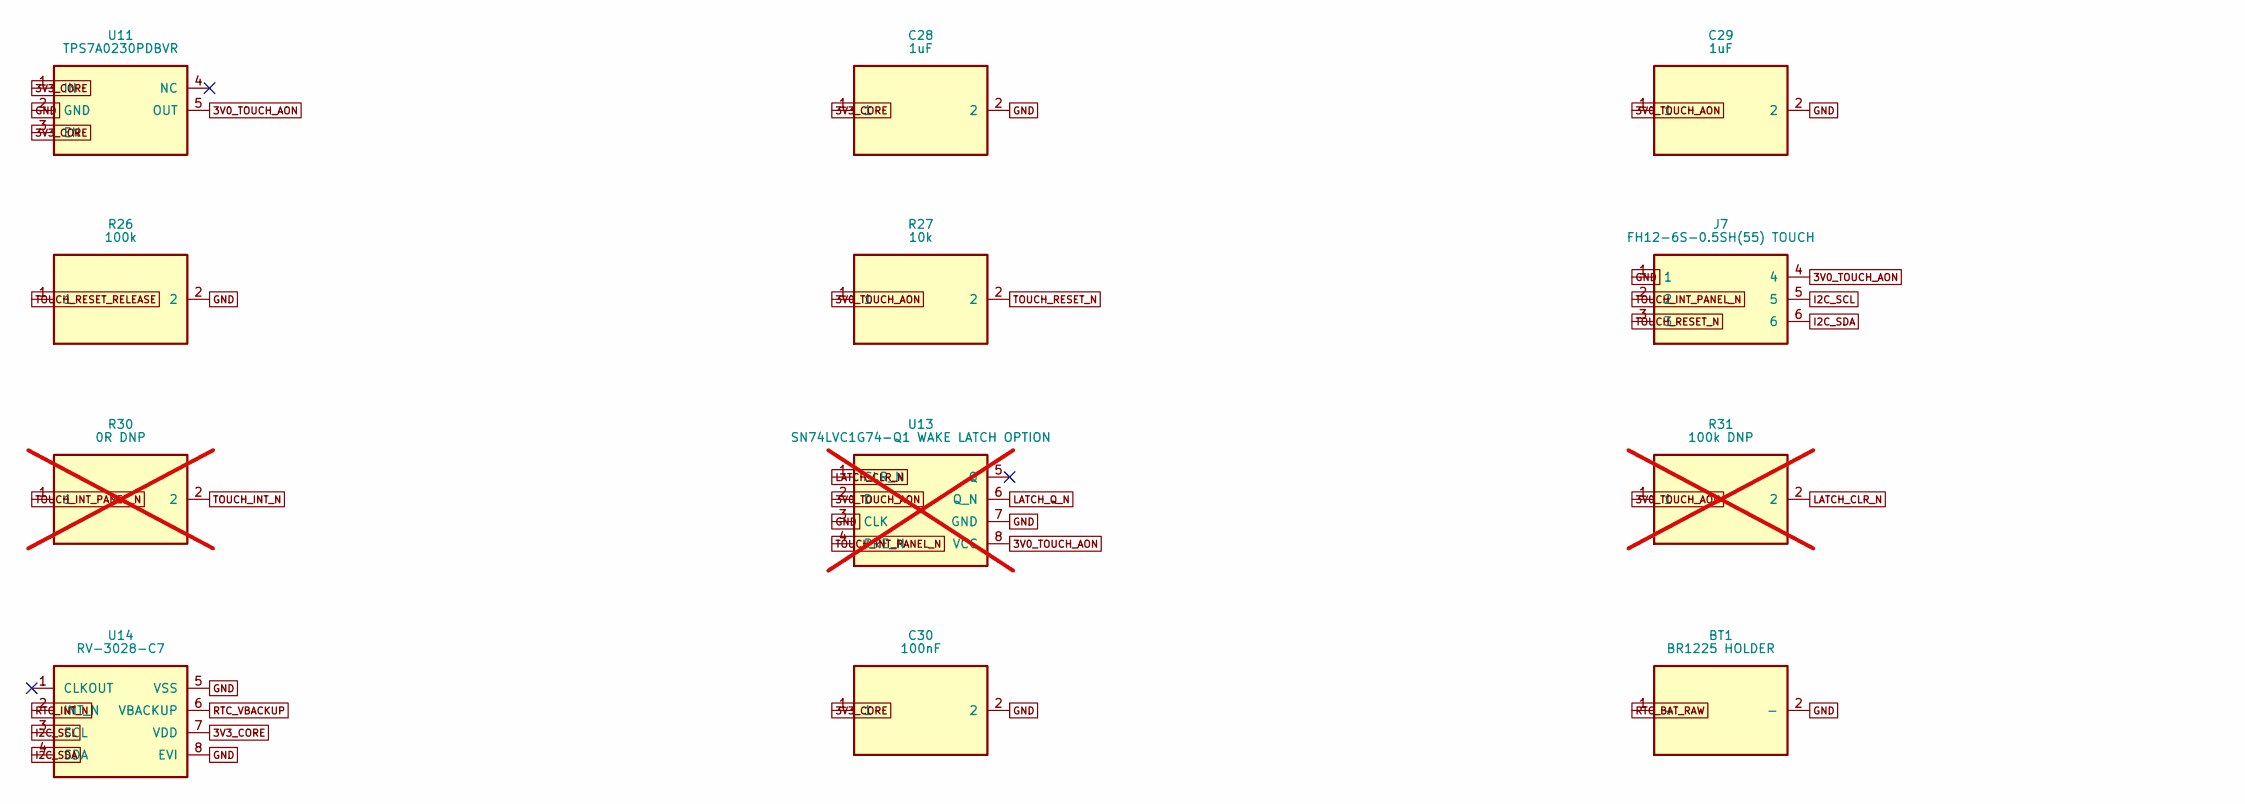
[picture p14: schematic 04_Touch_RTC.kicad_sch, part in row 1, column 1]

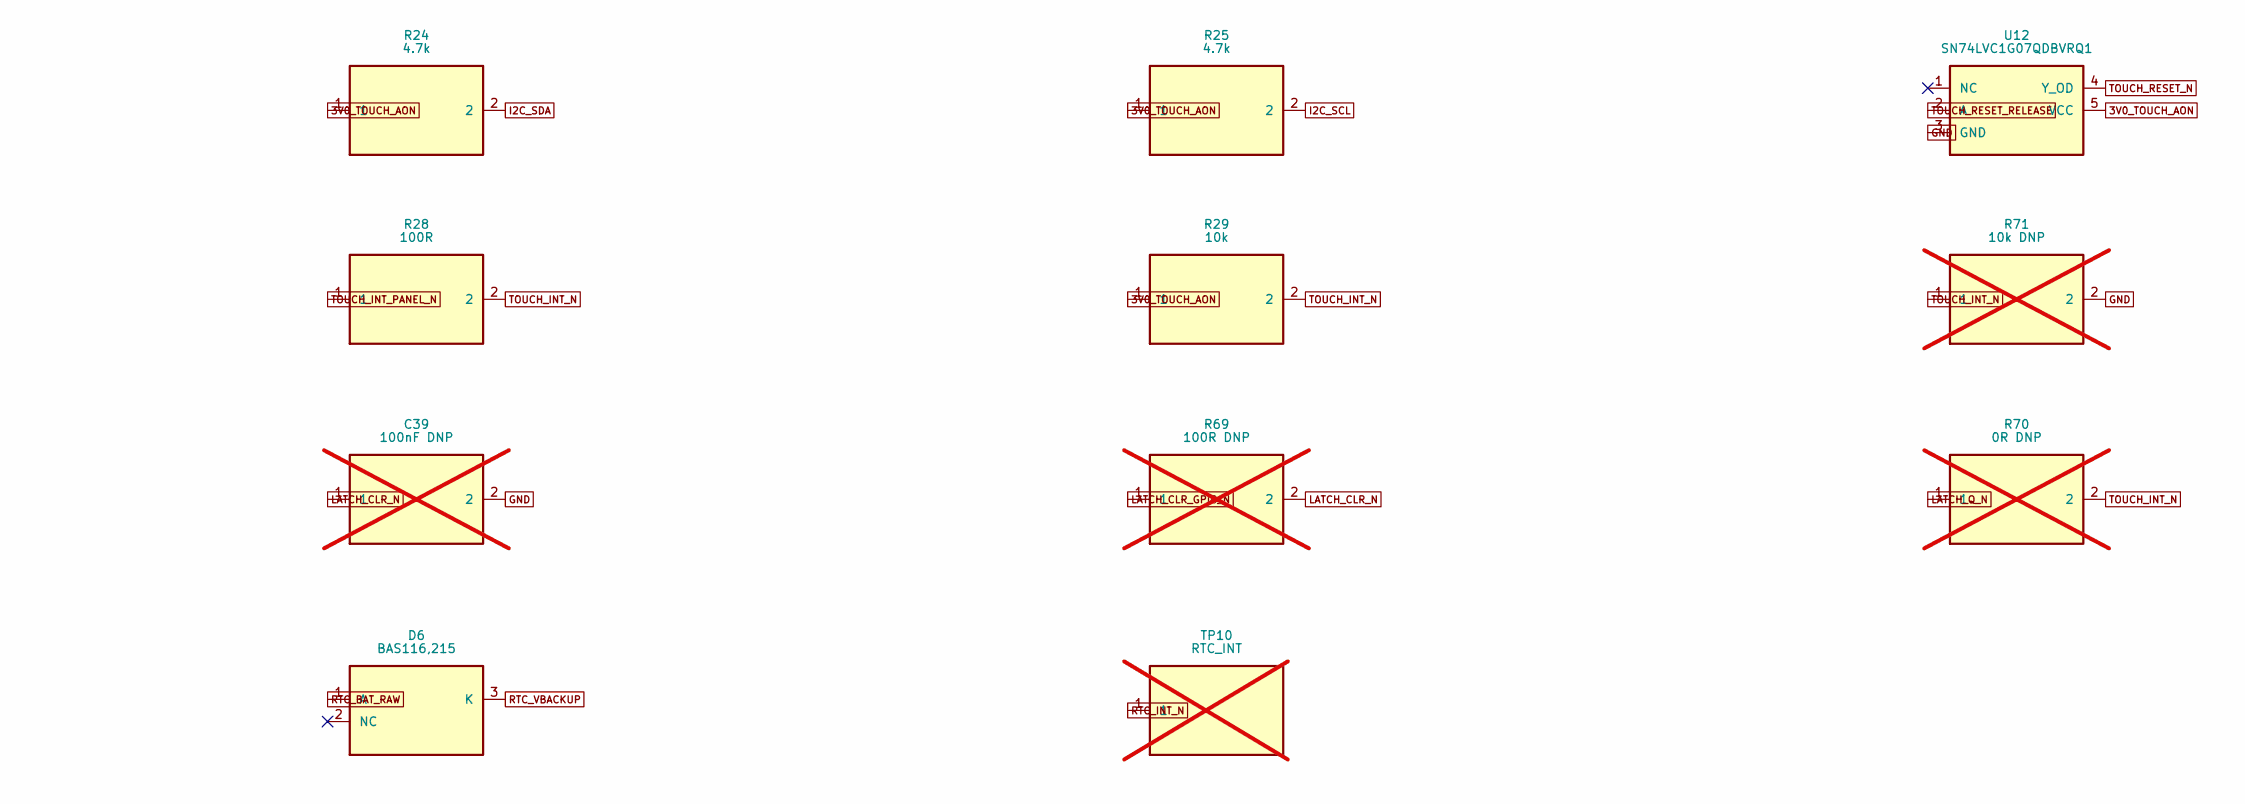
[picture p15: schematic 04_Touch_RTC.kicad_sch, part in row 1, column 2]

Parts:
BT1: BR1225 HOLDER; BatteryHolder_Keystone_500; MPN 500
C28, C29: 1uF; C_0603_1608Metric_Pad1.08x0.95mm_HandSolder
C30: 100nF; C_0603_1608Metric_Pad1.08x0.95mm_HandSolder
C39: 100nF DNP; C_0603_1608Metric_Pad1.08x0.95mm_HandSolder; not fitted
D6: BAS116,215; SOT-23; MPN BAS116,215
J7: FH12-6S-0.5SH(55) TOUCH; Hirose_FH12-6S-0.5SH_1x06-1MP_P0.50mm_Horizontal; MPN FH12-6S-0.5SH(55)
R24, R25: 4.7k; R_0603_1608Metric_Pad0.98x0.95mm_HandSolder
R26: 100k; R_0603_1608Metric_Pad0.98x0.95mm_HandSolder
R27, R29: 10k; R_0603_1608Metric_Pad0.98x0.95mm_HandSolder
R28: 100R; R_0603_1608Metric_Pad0.98x0.95mm_HandSolder
R30, R70: 0R DNP; R_0603_1608Metric_Pad0.98x0.95mm_HandSolder; not fitted
R31: 100k DNP; R_0603_1608Metric_Pad0.98x0.95mm_HandSolder; not fitted
R69: 100R DNP; R_0603_1608Metric_Pad0.98x0.95mm_HandSolder; not fitted
R71: 10k DNP; R_0603_1608Metric_Pad0.98x0.95mm_HandSolder; not fitted
TP10: RTC_INT; TestPoint_Pad_D1.0mm; not fitted
U11: TPS7A0230PDBVR; SOT-23-5; MPN TPS7A0230PDBVR
U12: SN74LVC1G07QDBVRQ1; SOT-23-5; MPN SN74LVC1G07QDBVRQ1
U13: SN74LVC1G74-Q1 WAKE LATCH OPTION; VSSOP-8_2.3x2mm_P0.5mm; MPN SN74LVC1G74QDCURQ1; not fitted
U14: RV-3028-C7; MPN RV-3028-C7-32.768kHz-1ppm-TA-QC

Connections:
3V0_TOUCH_AON: C29.1, J7.4, R24.1, R25.1, R27.1, R29.1, R31.1, U11.5 (OUT), U12.5 (VCC), U13.2 (D), U13.8 (VCC)
3V3_CORE: C28.1, C30.1, U11.1 (IN), U11.3 (EN), U14.7 (VDD)
GND: BT1.2 (-), C28.2, C29.2, C30.2, C39.2, J7.1, R26.2, R71.2, U11.2 (GND), U12.3 (GND), U13.3 (CLK), U13.7 (GND), U14.5 (VSS), U14.8 (EVI)
I2C_SCL: J7.5, R25.2, U14.3 (SCL)
I2C_SDA: J7.6, R24.2, U14.4 (SDA)
LATCH_CLR_GPIO_N: R69.1
LATCH_CLR_N: C39.1, R31.2, R69.2, U13.1 (CLR_N)
LATCH_Q_N: R70.1, U13.6 (Q_N)
RTC_BAT_RAW: BT1.1 (+), D6.1 (A)
RTC_INT_N: TP10.1, U14.2 (INT_N)
RTC_VBACKUP: D6.3 (K), U14.6 (VBACKUP)
TOUCH_INT_N: R28.2, R29.2, R30.2, R70.2, R71.1
TOUCH_INT_PANEL_N: J7.2, R28.1, R30.1, U13.4 (PRE_N)
TOUCH_RESET_N: J7.3, R27.2, U12.4 (Y_OD)
TOUCH_RESET_RELEASE: R26.1, U12.2 (A)
