fabianhartmann2/LandyHeater-Board/hardware/05_AUTOTERM_1Wire.kicad_sch

## KiCad design hardware/05_AUTOTERM_1Wire.kicad_sch (2026-09-07, an earlier design)

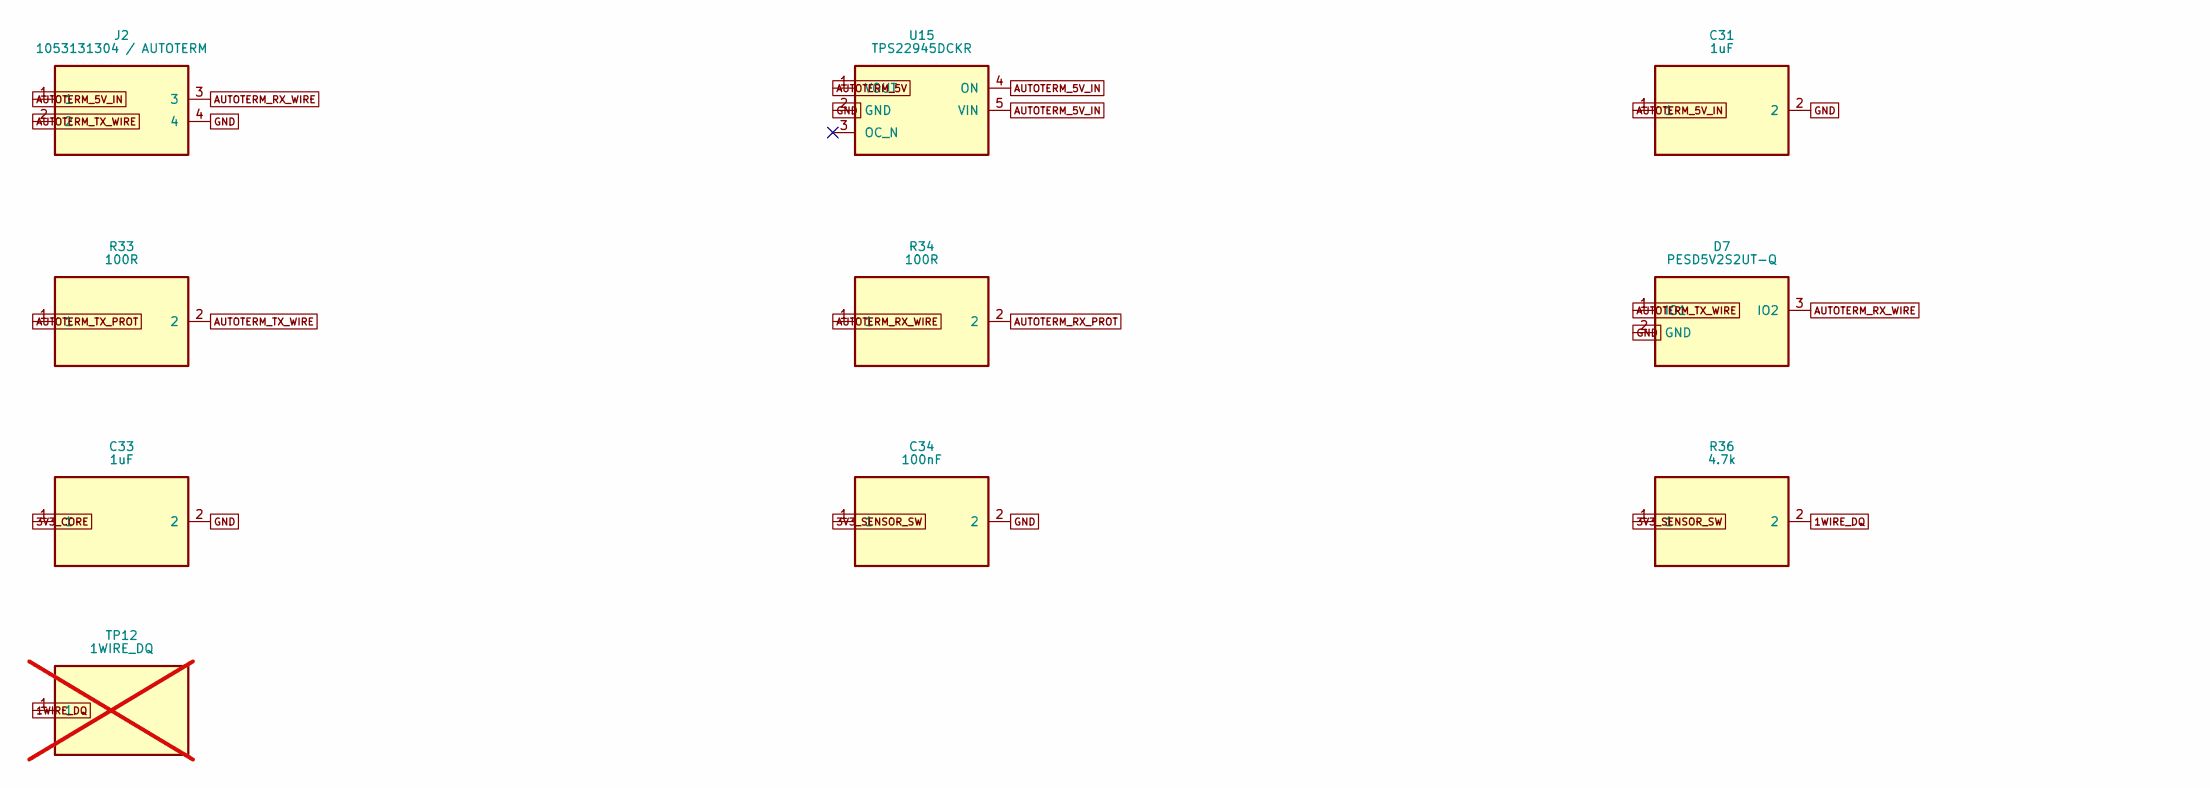
[picture p16: schematic 05_AUTOTERM_1Wire.kicad_sch, part in row 1, column 1]

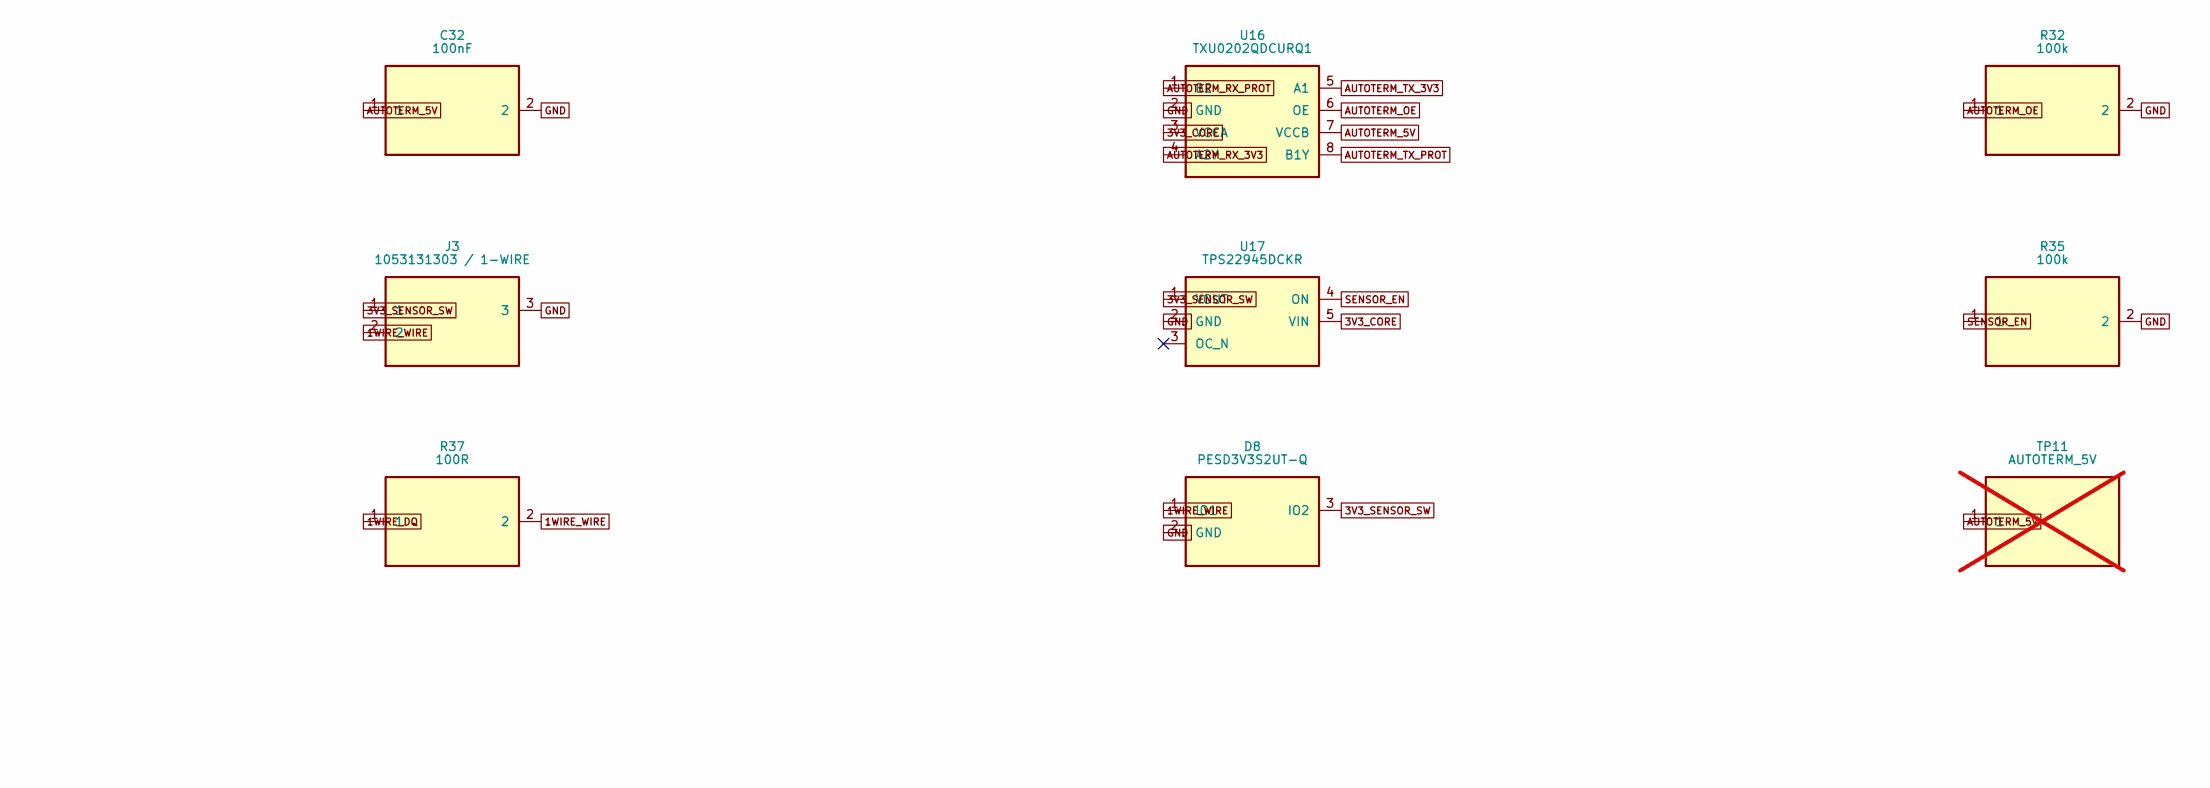
[picture p17: schematic 05_AUTOTERM_1Wire.kicad_sch, part in row 1, column 2]

Parts:
C31, C33: 1uF; C_0603_1608Metric_Pad1.08x0.95mm_HandSolder
C32, C34: 100nF; C_0603_1608Metric_Pad1.08x0.95mm_HandSolder
D7: PESD5V2S2UT-Q; SOT-23; MPN PESD5V2S2UT-Q
D8: PESD3V3S2UT-Q; SOT-23; MPN PESD3V3S2UT-Q
J2: 1053131304 / AUTOTERM; Molex_Nano-Fit_105313-xx04_1x04_P2.50mm_Horizontal; MPN 1053131304
J3: 1053131303 / 1-WIRE; Molex_Nano-Fit_105313-xx03_1x03_P2.50mm_Horizontal; MPN 1053131303
R32, R35: 100k; R_0603_1608Metric_Pad0.98x0.95mm_HandSolder
R33, R34, R37: 100R; R_0603_1608Metric_Pad0.98x0.95mm_HandSolder
R36: 4.7k; R_0603_1608Metric_Pad0.98x0.95mm_HandSolder
TP11: AUTOTERM_5V; TestPoint_Pad_D1.0mm; not fitted
TP12: 1WIRE_DQ; TestPoint_Pad_D1.0mm; not fitted
U15, U17: TPS22945DCKR; SOT-353_SC-70-5; MPN TPS22945DCKR
U16: TXU0202QDCURQ1; VSSOP-8_2.3x2mm_P0.5mm; MPN TXU0202QDCURQ1

Connections:
1WIRE_DQ: R36.2, R37.1, TP12.1
1WIRE_WIRE: D8.1 (IO1), J3.2, R37.2
3V3_CORE: C33.1, U16.3 (VCCA), U17.5 (VIN)
3V3_SENSOR_SW: C34.1, D8.3 (IO2), J3.1, R36.1, U17.1 (VOUT)
AUTOTERM_5V: C32.1, TP11.1, U15.1 (VOUT), U16.7 (VCCB)
AUTOTERM_5V_IN: C31.1, J2.1, U15.4 (ON), U15.5 (VIN)
AUTOTERM_OE: R32.1, U16.6 (OE)
AUTOTERM_RX_3V3: U16.4 (A2Y)
AUTOTERM_RX_PROT: R34.2, U16.1 (B2)
AUTOTERM_RX_WIRE: D7.3 (IO2), J2.3, R34.1
AUTOTERM_TX_3V3: U16.5 (A1)
AUTOTERM_TX_PROT: R33.1, U16.8 (B1Y)
AUTOTERM_TX_WIRE: D7.1 (IO1), J2.2, R33.2
GND: C31.2, C32.2, C33.2, C34.2, D7.2 (GND), D8.2 (GND), J2.4, J3.3, R32.2, R35.2, U15.2 (GND), U16.2 (GND), U17.2 (GND)
SENSOR_EN: R35.1, U17.4 (ON)
