fabianhartmann2/LandyHeater-Board/hardware/06_Controls_Diagnostics.kicad_sch

## KiCad design hardware/06_Controls_Diagnostics.kicad_sch (2026-09-07, an earlier design)

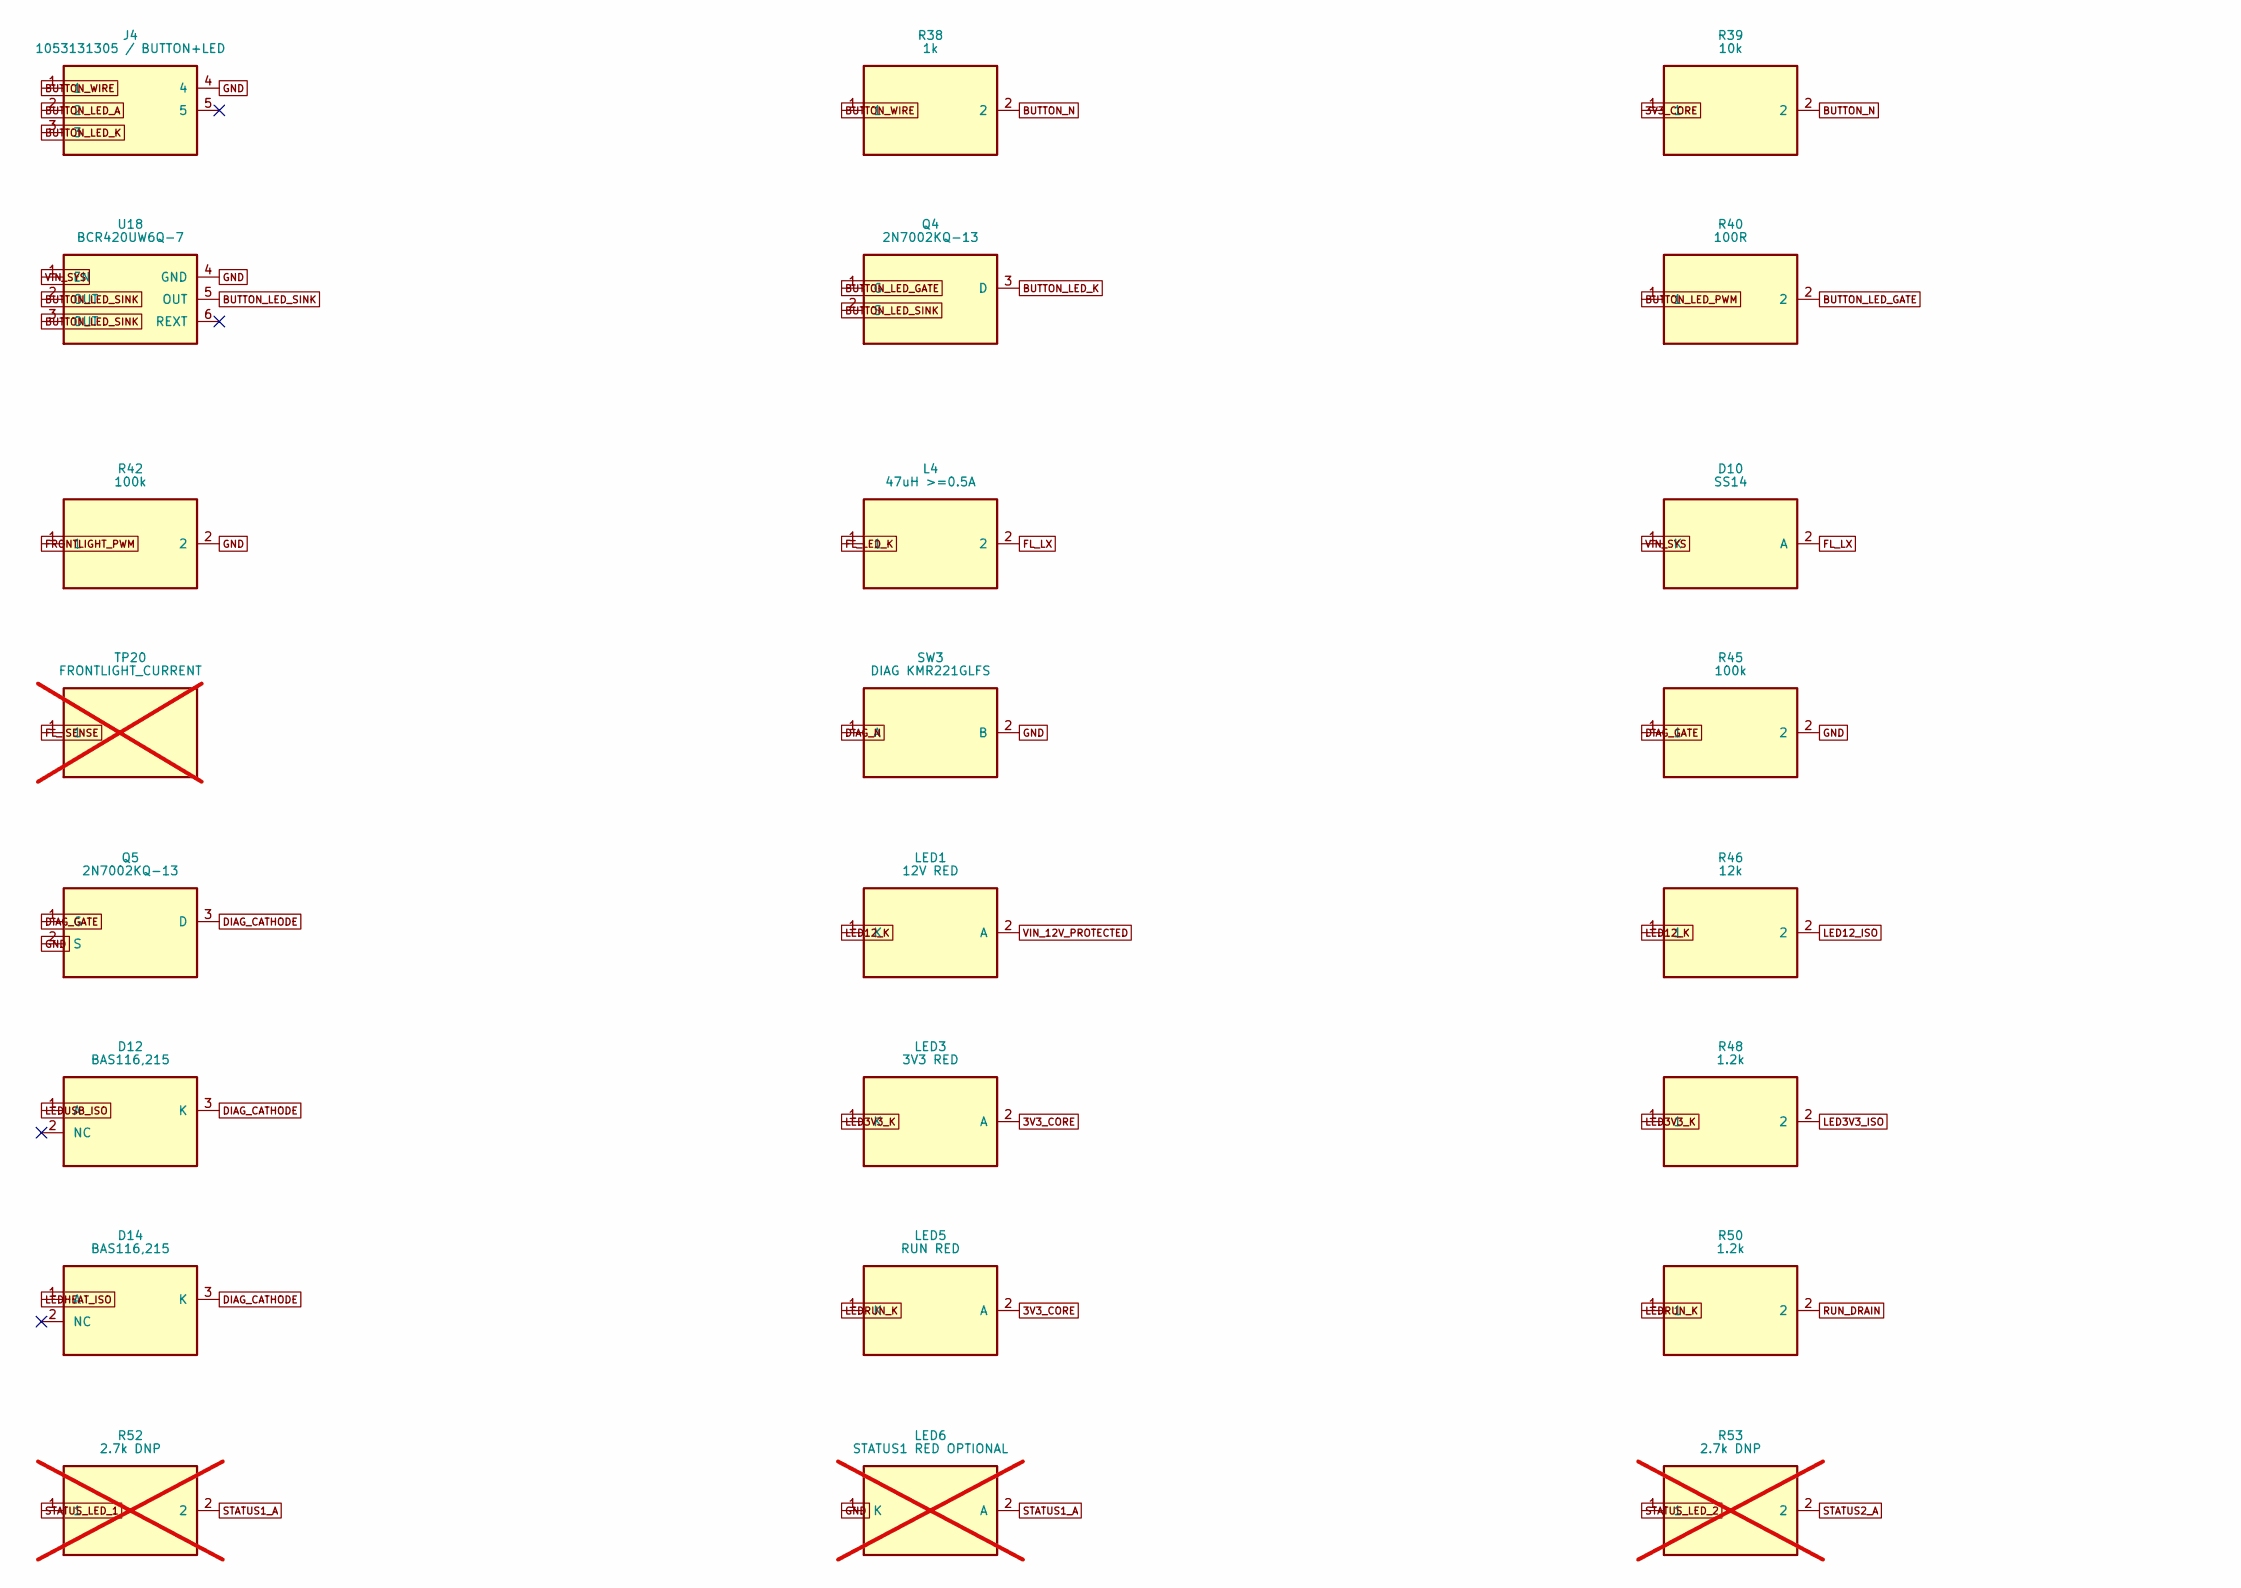
[picture p18: schematic 06_Controls_Diagnostics.kicad_sch, part in row 1, column 1]

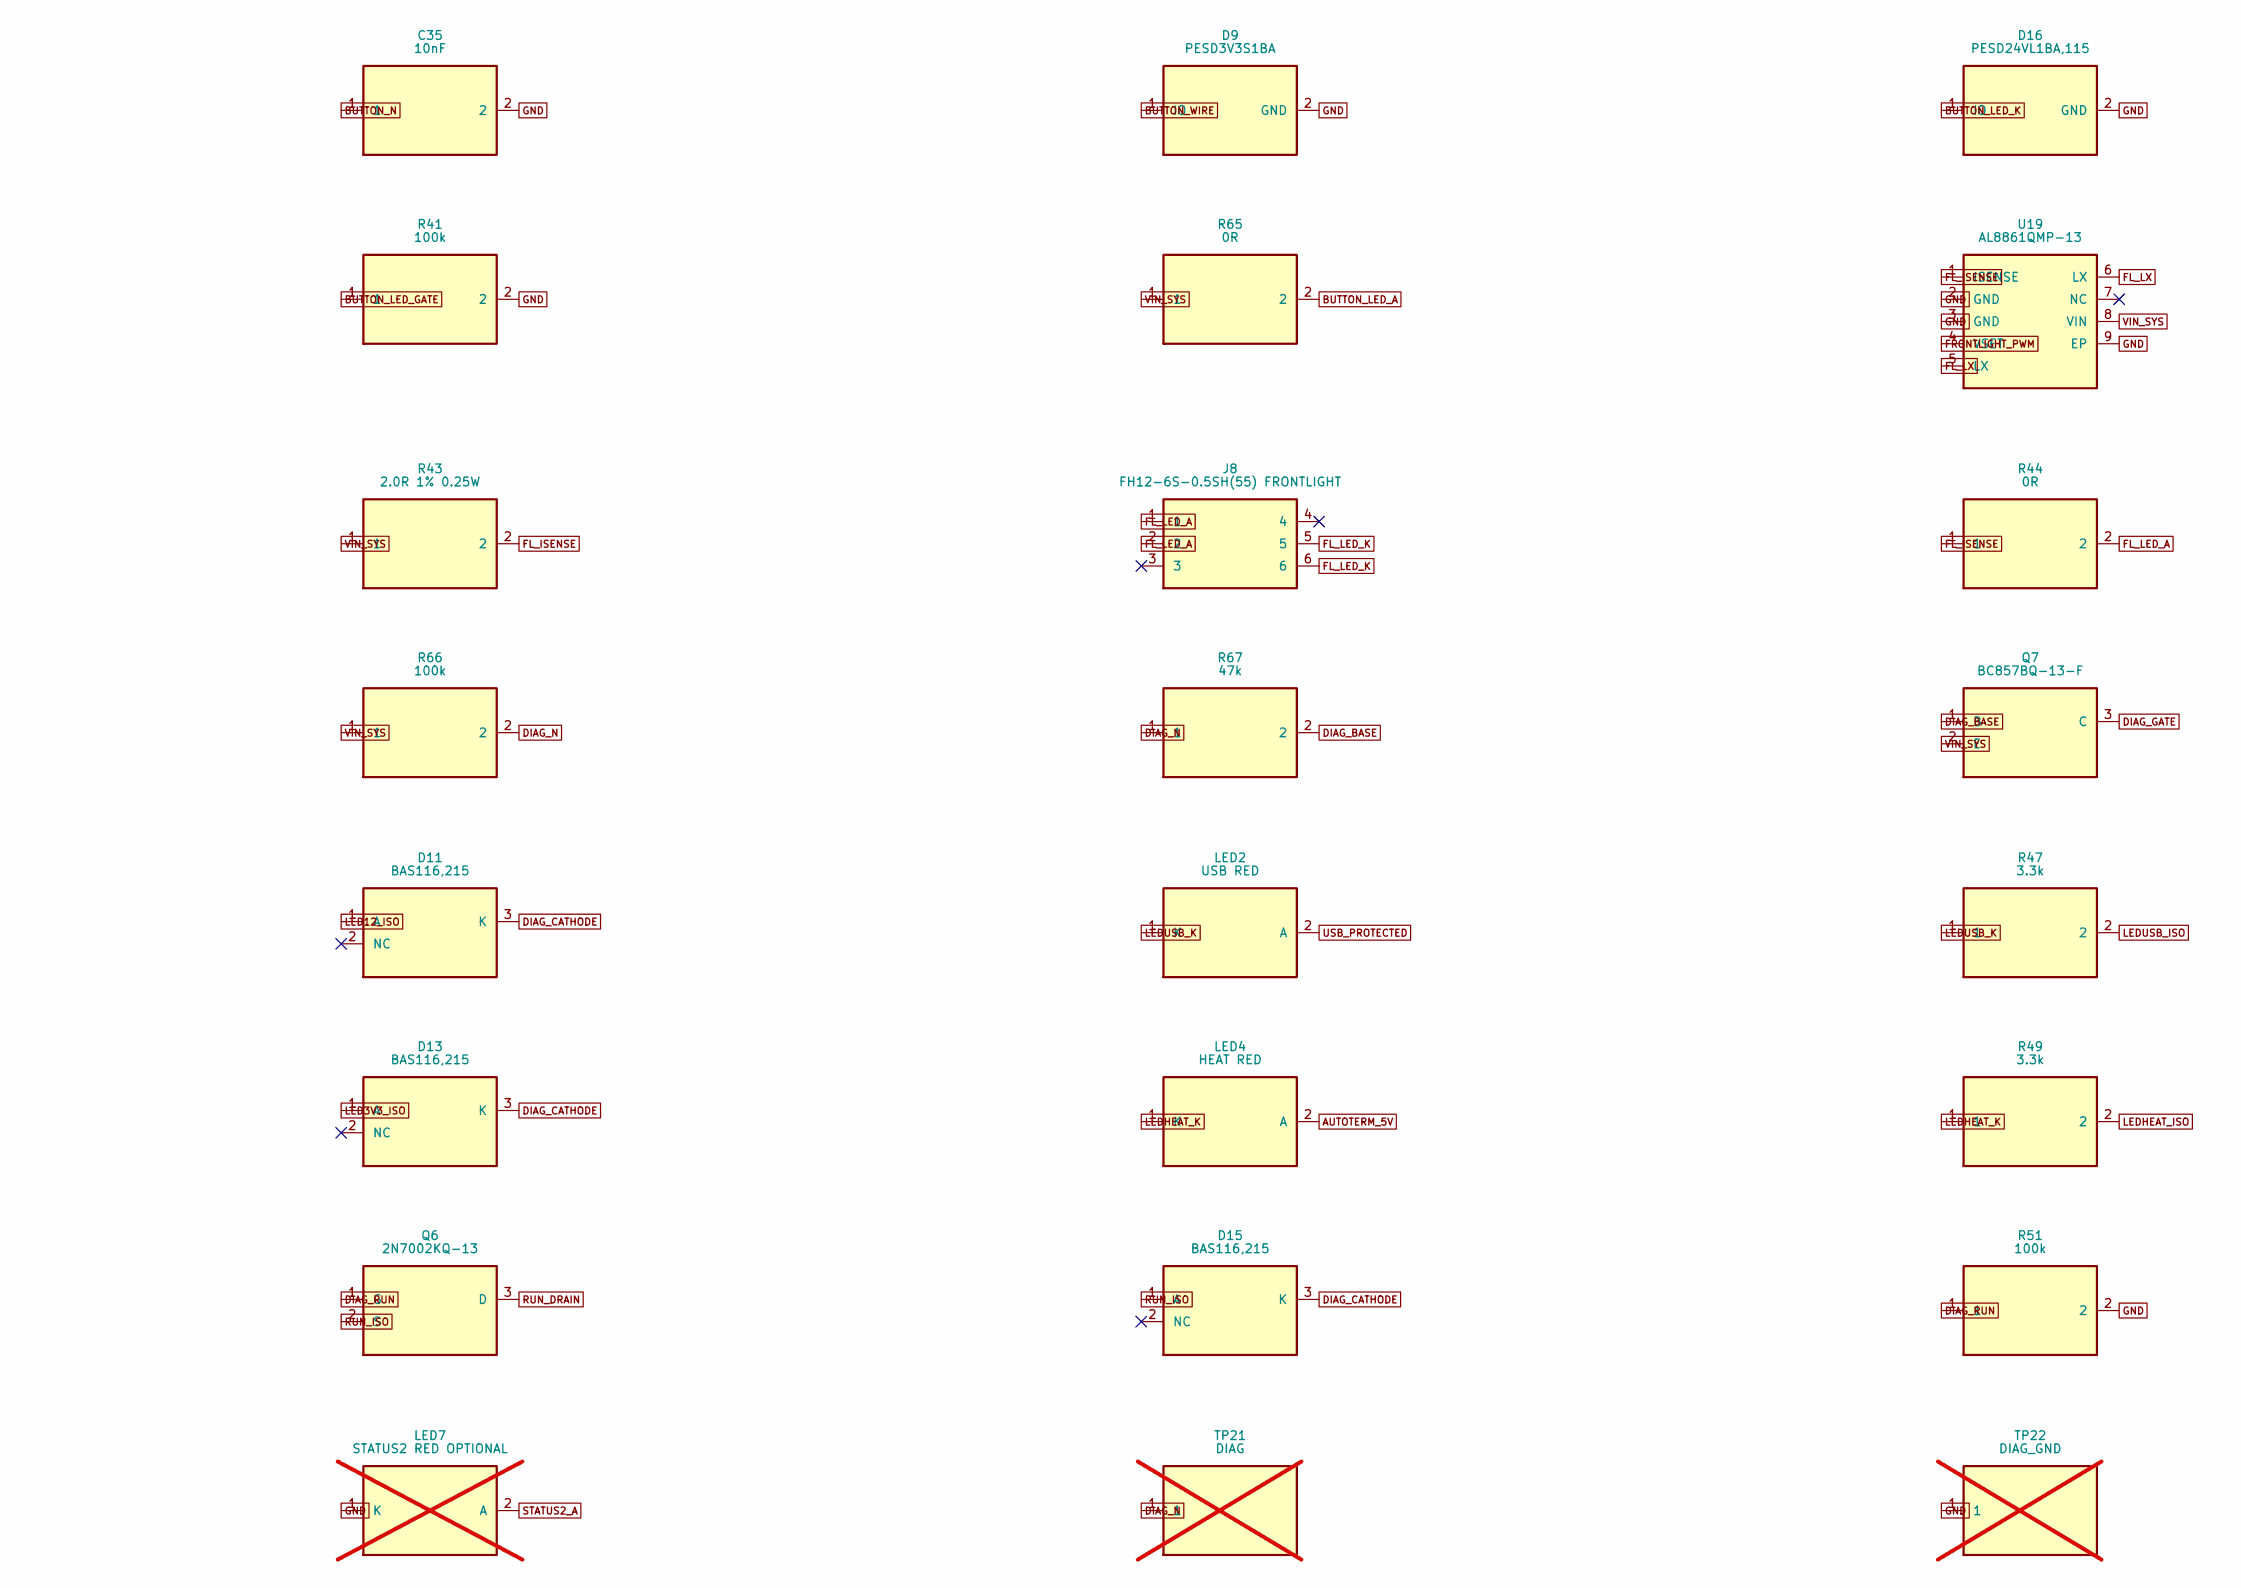
[picture p19: schematic 06_Controls_Diagnostics.kicad_sch, part in row 1, column 2]

Parts:
C35: 10nF; C_0603_1608Metric_Pad1.08x0.95mm_HandSolder
D9: PESD3V3S1BA; D_SOD-323; MPN PESD3V3S1BA
D10: SS14; D_SMA
D11, D12, D13, D14, D15: BAS116,215; SOT-23; MPN BAS116,215
D16: PESD24VL1BA,115; D_SOD-323; MPN PESD24VL1BA,115
J4: 1053131305 / BUTTON+LED; Molex_Nano-Fit_105313-xx05_1x05_P2.50mm_Horizontal; MPN 1053131305
J8: FH12-6S-0.5SH(55) FRONTLIGHT; Hirose_FH12-6S-0.5SH_1x06-1MP_P0.50mm_Horizontal; MPN FH12-6S-0.5SH(55)
L4: 47uH >=0.5A; L_Coilcraft_XAL4020-XXX
LED1: 12V RED; LED_0603_1608Metric; MPN LTST-C190KRKT
LED2: USB RED; LED_0603_1608Metric; MPN LTST-C190KRKT
LED3: 3V3 RED; LED_0603_1608Metric; MPN LTST-C190KRKT
LED4: HEAT RED; LED_0603_1608Metric; MPN LTST-C190KRKT
LED5: RUN RED; LED_0603_1608Metric; MPN LTST-C190KRKT
LED6: STATUS1 RED OPTIONAL; LED_0603_1608Metric; MPN LTST-C190KRKT; not fitted
LED7: STATUS2 RED OPTIONAL; LED_0603_1608Metric; MPN LTST-C190KRKT; not fitted
Q4, Q5, Q6: 2N7002KQ-13; SOT-23; MPN 2N7002KQ-13
Q7: BC857BQ-13-F; SOT-23; MPN BC857BQ-13-F
R38: 1k; R_0603_1608Metric_Pad0.98x0.95mm_HandSolder
R39: 10k; R_0603_1608Metric_Pad0.98x0.95mm_HandSolder
R40: 100R; R_0603_1608Metric_Pad0.98x0.95mm_HandSolder
R41, R42, R45, R51, R66: 100k; R_0603_1608Metric_Pad0.98x0.95mm_HandSolder
R43: 2.0R 1% 0.25W; R_1206_3216Metric_Pad1.30x1.75mm_HandSolder
R44, R65: 0R; R_0603_1608Metric_Pad0.98x0.95mm_HandSolder
R46: 12k; R_0603_1608Metric_Pad0.98x0.95mm_HandSolder
R47, R49: 3.3k; R_0603_1608Metric_Pad0.98x0.95mm_HandSolder
R48, R50: 1.2k; R_0603_1608Metric_Pad0.98x0.95mm_HandSolder
R52, R53: 2.7k DNP; R_0603_1608Metric_Pad0.98x0.95mm_HandSolder; not fitted
R67: 47k; R_0603_1608Metric_Pad0.98x0.95mm_HandSolder
SW3: DIAG KMR221GLFS; SW_Push_1P1T_NO_CK_KMR2; MPN KMR221GLFS
TP20: FRONTLIGHT_CURRENT; TestPoint_Pad_D1.0mm; not fitted
TP21: DIAG; TestPoint_Pad_D1.0mm; not fitted
TP22: DIAG_GND; TestPoint_Pad_D1.0mm; not fitted
U18: BCR420UW6Q-7; SOT-23-6; MPN BCR420UW6Q-7
U19: AL8861QMP-13; MSOP-8-1EP_3x3mm_P0.65mm_EP1.5x1.8mm; MPN AL8861QMP-13

Connections:
3V3_CORE: LED3.2 (A), LED5.2 (A), R39.1
AUTOTERM_5V: LED4.2 (A)
BUTTON_LED_A: J4.2, R65.2
BUTTON_LED_GATE: Q4.1 (G), R40.2, R41.1
BUTTON_LED_K: D16.1 (IO), J4.3, Q4.3 (D)
BUTTON_LED_PWM: R40.1
BUTTON_LED_SINK: Q4.2 (S), U18.2 (OUT), U18.3 (OUT), U18.5 (OUT)
BUTTON_N: C35.1, R38.2, R39.2
BUTTON_WIRE: D9.1 (IO), J4.1, R38.1
DIAG_BASE: Q7.1 (B), R67.2
DIAG_CATHODE: D11.3 (K), D12.3 (K), D13.3 (K), D14.3 (K), D15.3 (K), Q5.3 (D)
DIAG_GATE: Q5.1 (G), Q7.3 (C), R45.1
DIAG_N: R66.2, R67.1, SW3.1 (A), TP21.1
DIAG_RUN: Q6.1 (G), R51.1
FL_ISENSE: R43.2, R44.1, TP20.1, U19.1 (ISENSE)
FL_LED_A: J8.1, J8.2, R44.2
FL_LED_K: J8.5, J8.6, L4.1
FL_LX: D10.2 (A), L4.2, U19.5 (LX), U19.6 (LX)
FRONTLIGHT_PWM: R42.1, U19.4 (VSET)
GND: C35.2, D9.2 (GND), D16.2 (GND), J4.4, LED6.1 (K), LED7.1 (K), Q5.2 (S), R41.2, R42.2, R45.2, R51.2, SW3.2 (B), TP22.1, U18.4 (GND), U19.2 (GND), U19.3 (GND), U19.9 (EP)
LED3V3_ISO: D13.1 (A), R48.2
LED3V3_K: LED3.1 (K), R48.1
LED12_ISO: D11.1 (A), R46.2
LED12_K: LED1.1 (K), R46.1
LEDHEAT_ISO: D14.1 (A), R49.2
LEDHEAT_K: LED4.1 (K), R49.1
LEDRUN_K: LED5.1 (K), R50.1
LEDUSB_ISO: D12.1 (A), R47.2
LEDUSB_K: LED2.1 (K), R47.1
RUN_DRAIN: Q6.3 (D), R50.2
RUN_ISO: D15.1 (A), Q6.2 (S)
STATUS1_A: LED6.2 (A), R52.2
STATUS2_A: LED7.2 (A), R53.2
STATUS_LED_1: R52.1
STATUS_LED_2: R53.1
USB_PROTECTED: LED2.2 (A)
VIN_12V_PROTECTED: LED1.2 (A)
VIN_SYS: D10.1 (K), Q7.2 (E), R43.1, R65.1, R66.1, U18.1 (EN), U19.8 (VIN)
